OLIMEX/ESP32-P4-PC/DOCUMENTS/ESP32-P4-PC-3.jpg

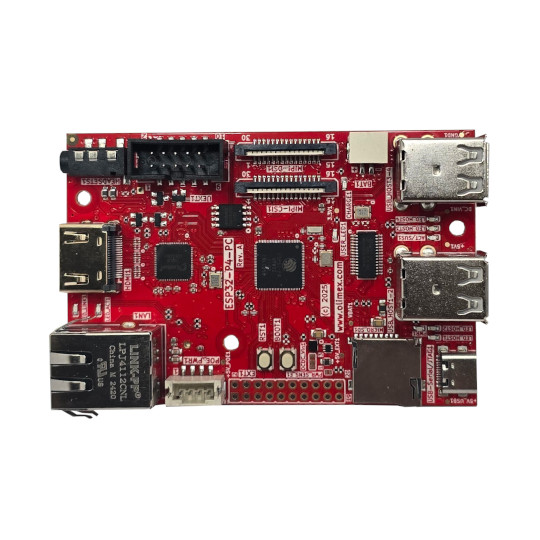
DOCUMENTS/ESP32-P4-PC-3.jpg
