OLIMEX/ESP32-P4-PC/SOFTWARE/ESP-IDF/p4_production_test/components/esp-bsp/bsp/esp32_azure_iot_kit/doc/esp32_azure_iot_kit.webp

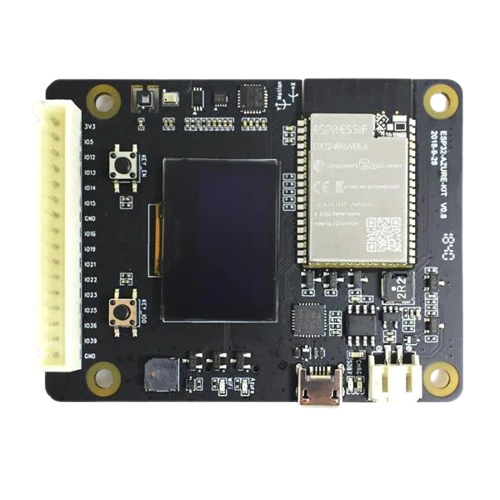
SOFTWARE/ESP-IDF/p4_production_test/components/esp-bsp/bsp/esp32_azure_iot_kit/doc/esp32_azure_iot_kit.webp
