OLIMEX/ESP32-P4-PC/SOFTWARE/ESP-IDF/p4_production_test/components/esp-bsp/bsp/esp32_azure_iot_kit/image.png

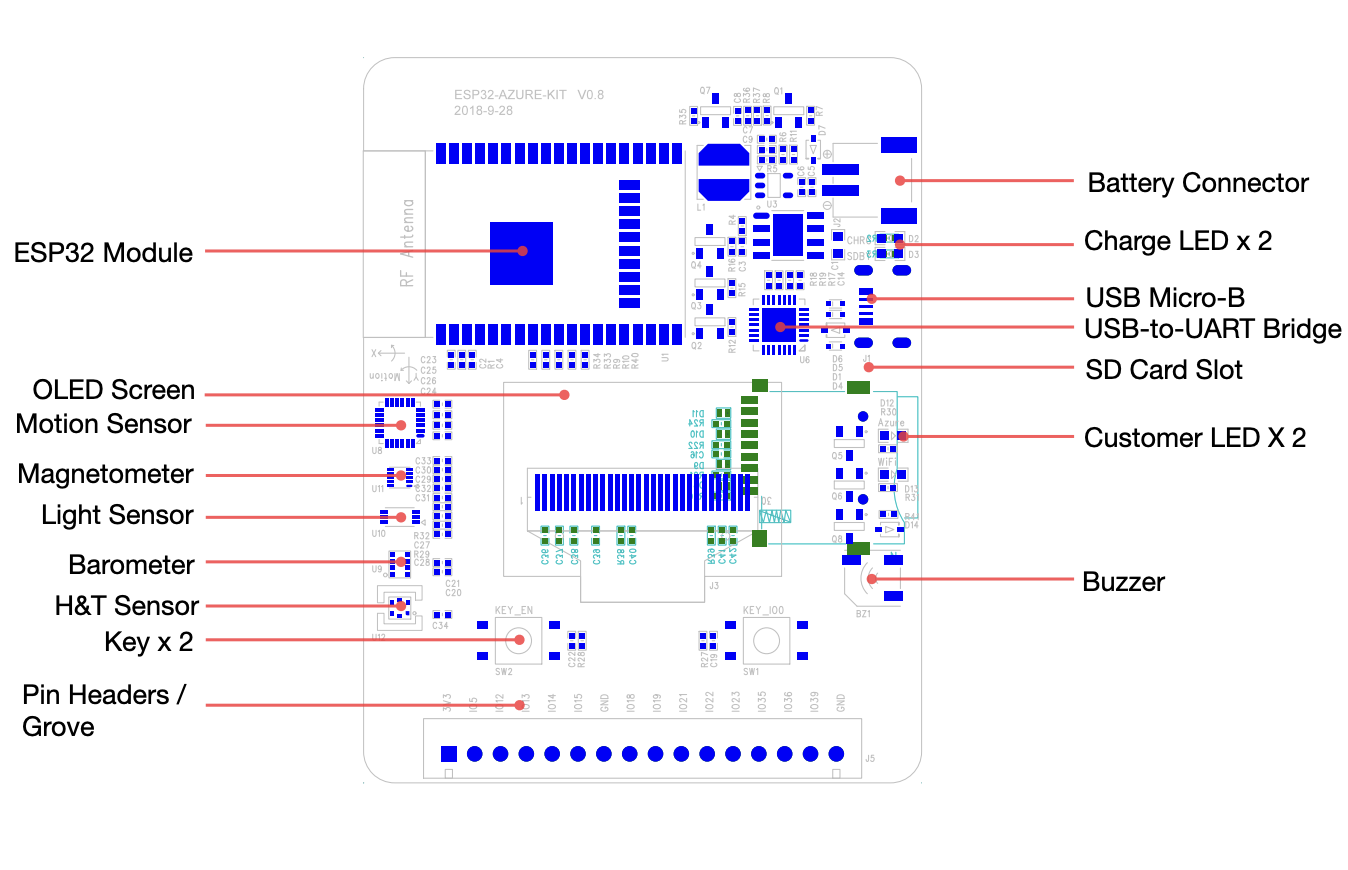
SOFTWARE/ESP-IDF/p4_production_test/components/esp-bsp/bsp/esp32_azure_iot_kit/image.png
