OLIMEX/ESP32-P4-PC/SOFTWARE/ESP-IDF/p4_production_test/components/esp-bsp/bsp/esp32_lyrat/doc/esp32_lyrat.webp

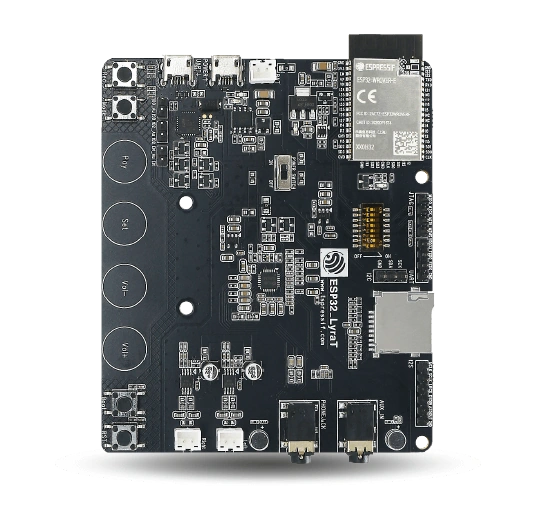
SOFTWARE/ESP-IDF/p4_production_test/components/esp-bsp/bsp/esp32_lyrat/doc/esp32_lyrat.webp
