OLIMEX/ESP32-P4-PC/SOFTWARE/ESP-IDF/p4_production_test/components/esp-bsp/bsp/esp32_lyrat/pic.jpg

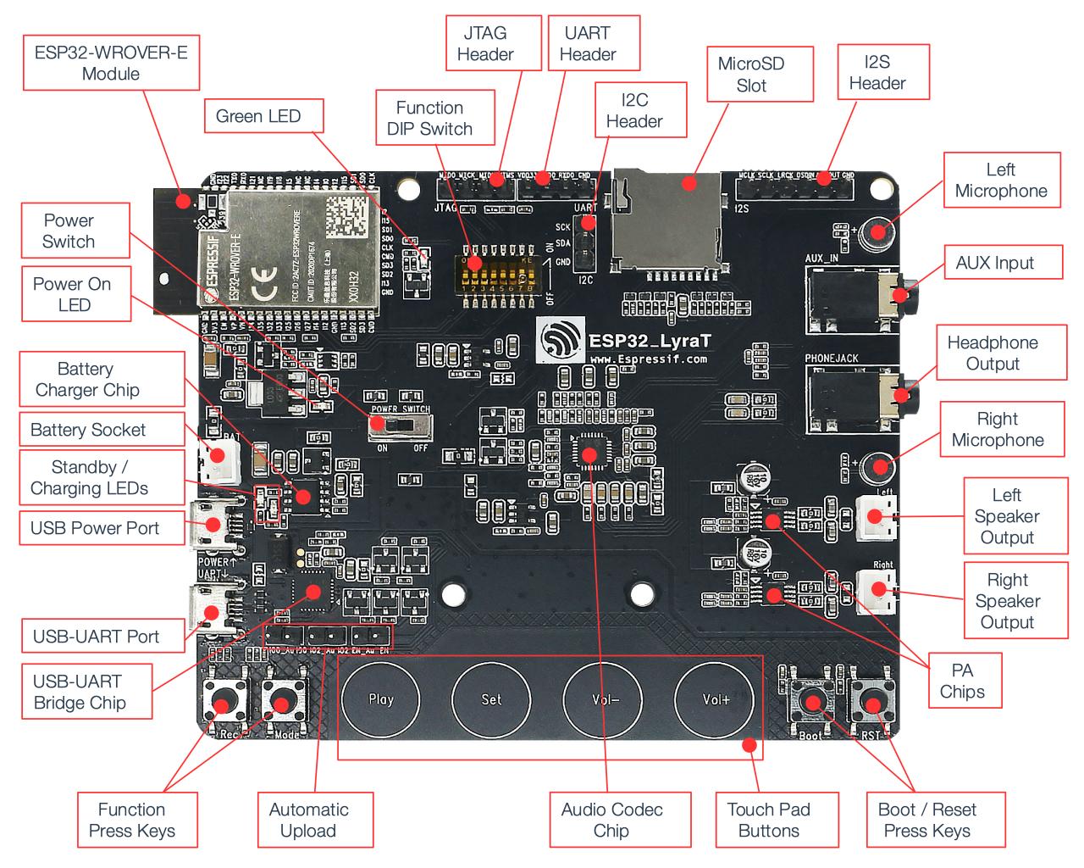
SOFTWARE/ESP-IDF/p4_production_test/components/esp-bsp/bsp/esp32_lyrat/pic.jpg
