OLIMEX/ESP32-P4-PC/SOFTWARE/ESP-IDF/p4_production_test/components/esp-bsp/bsp/esp32_p4_eye/doc/esp32_p4_eye.webp

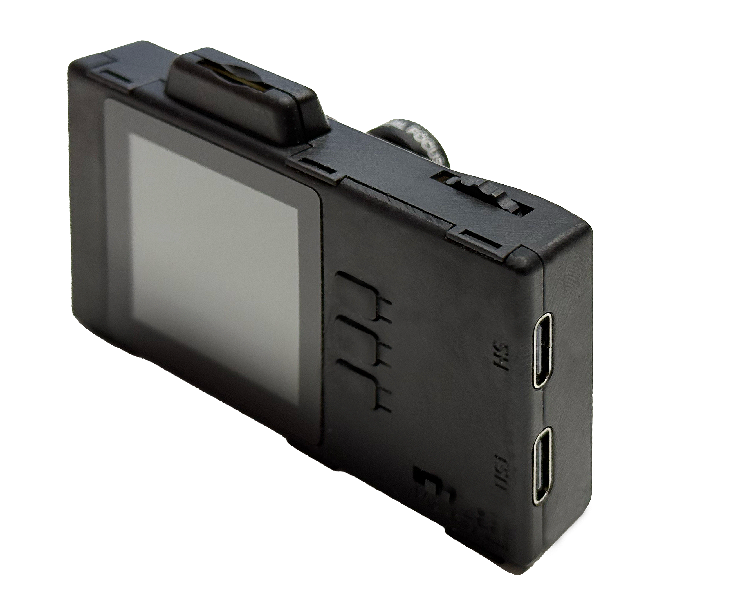
SOFTWARE/ESP-IDF/p4_production_test/components/esp-bsp/bsp/esp32_p4_eye/doc/esp32_p4_eye.webp
