OLIMEX/ESP32-P4-PC/SOFTWARE/ESP-IDF/p4_production_test/components/esp-bsp/bsp/esp32_s2_kaluga_kit/doc/esp32_s2_kaluga_kit.webp

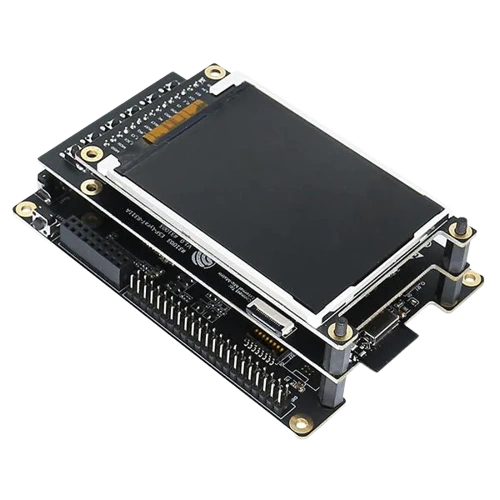
SOFTWARE/ESP-IDF/p4_production_test/components/esp-bsp/bsp/esp32_s2_kaluga_kit/doc/esp32_s2_kaluga_kit.webp
