OLIMEX/ESP32-P4-PC/SOFTWARE/ESP-IDF/p4_production_test/components/esp-bsp/bsp/esp32_s3_korvo_1/doc/esp32_s3_korvo_1.webp

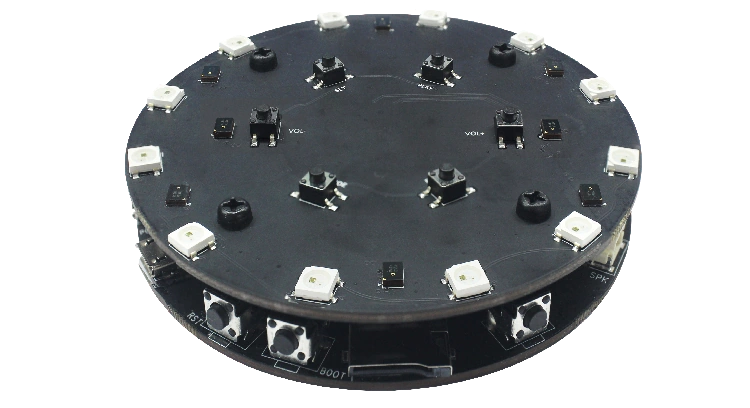
SOFTWARE/ESP-IDF/p4_production_test/components/esp-bsp/bsp/esp32_s3_korvo_1/doc/esp32_s3_korvo_1.webp
