OLIMEX/ESP32-P4-PC/SOFTWARE/ESP-IDF/p4_production_test/components/esp-bsp/bsp/esp32_s3_lcd_ev_board/doc/esp32_s3_lcd_ev_board.webp

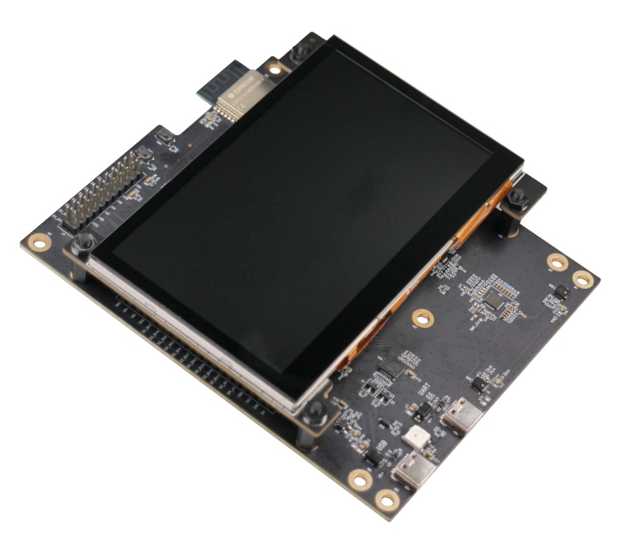
SOFTWARE/ESP-IDF/p4_production_test/components/esp-bsp/bsp/esp32_s3_lcd_ev_board/doc/esp32_s3_lcd_ev_board.webp
