OLIMEX/ESP32-P4-PC/SOFTWARE/ESP-IDF/p4_production_test/components/esp-bsp/bsp/esp_wrover_kit/doc/esp-wrover-kit-v4.1-layout-front.png

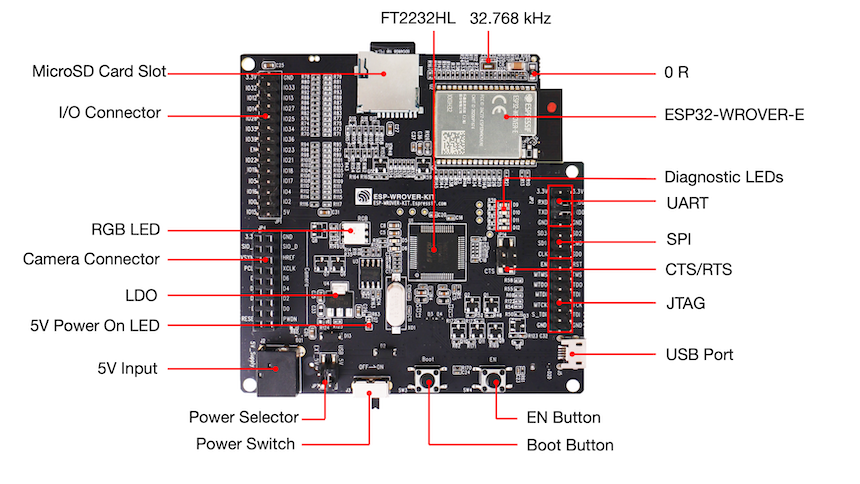
SOFTWARE/ESP-IDF/p4_production_test/components/esp-bsp/bsp/esp_wrover_kit/doc/esp-wrover-kit-v4.1-layout-front.png
