OLIMEX/ESP32-P4-PC/SOFTWARE/ESP-IDF/p4_production_test/components/esp-bsp/bsp/esp_wrover_kit/doc/esp_wrover_kit.webp

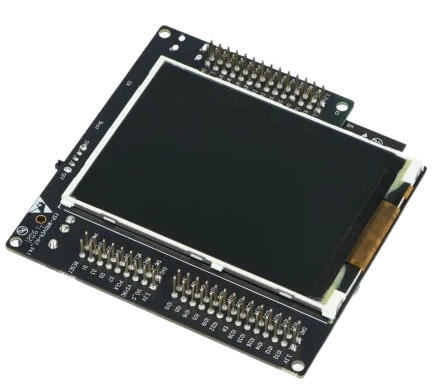
SOFTWARE/ESP-IDF/p4_production_test/components/esp-bsp/bsp/esp_wrover_kit/doc/esp_wrover_kit.webp
