OLIMEX/ESP32-P4-PC/SOFTWARE/ESP-IDF/p4_production_test/components/esp-bsp/bsp/m5_atom_s3/doc/m5_atom_s3.webp

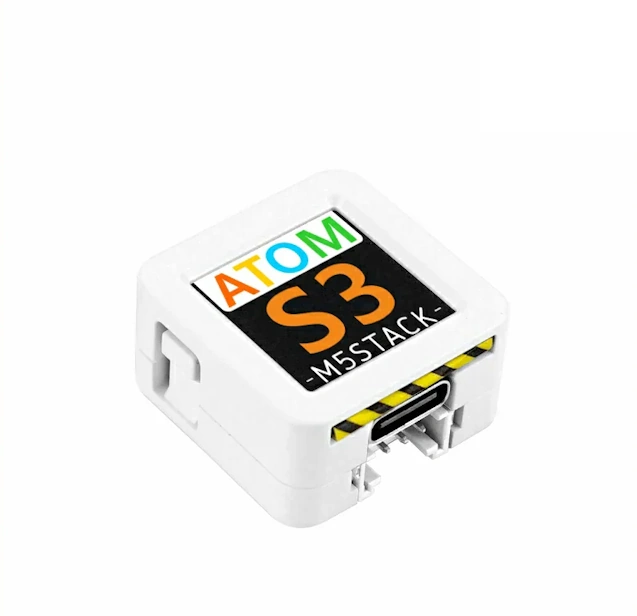
SOFTWARE/ESP-IDF/p4_production_test/components/esp-bsp/bsp/m5_atom_s3/doc/m5_atom_s3.webp
