OLIMEX/ESP32-P4-PC/SOFTWARE/ESP-IDF/p4_production_test/components/esp-bsp/bsp/m5dial/doc/m5dial.webp

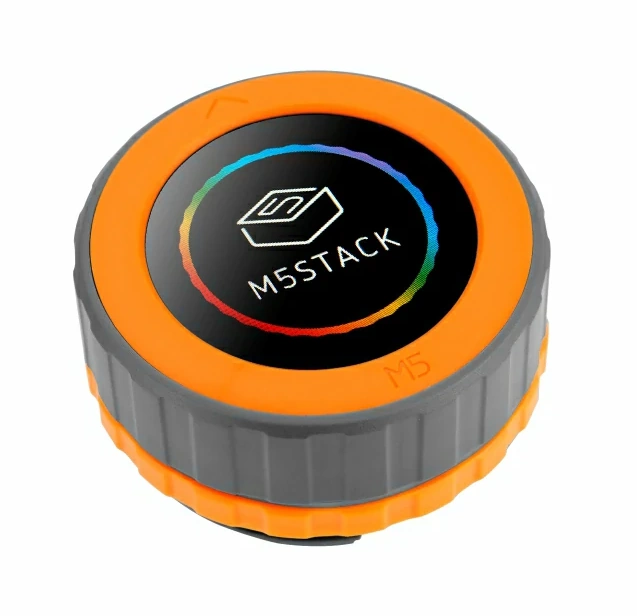
SOFTWARE/ESP-IDF/p4_production_test/components/esp-bsp/bsp/m5dial/doc/m5dial.webp
