OLIMEX/ESP32-P4-PC/SOFTWARE/ESP-IDF/p4_production_test/components/esp-bsp/bsp/m5dial/doc/pic.webp

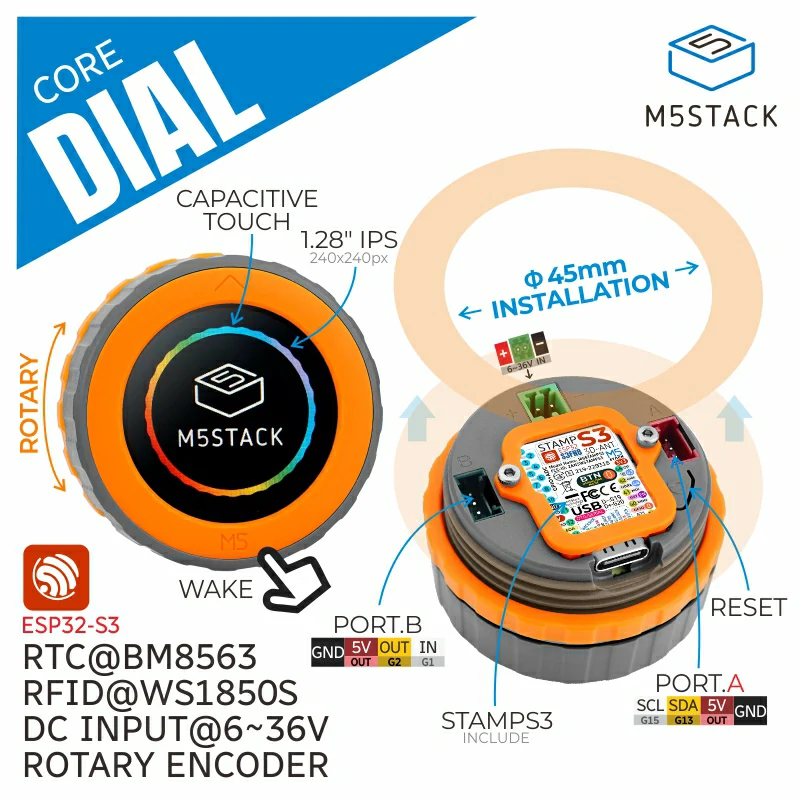
SOFTWARE/ESP-IDF/p4_production_test/components/esp-bsp/bsp/m5dial/doc/pic.webp
