OLIMEX/ESP32-P4-PC/SOFTWARE/ESP-IDF/p4_production_test/components/esp-bsp/bsp/m5stack_core_s3/doc/pic.webp

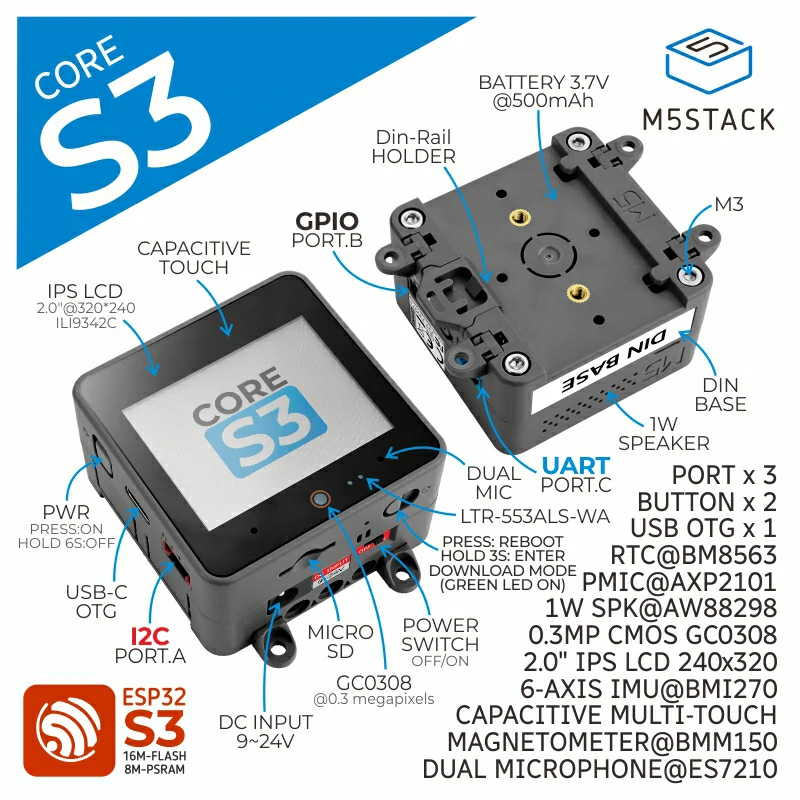
SOFTWARE/ESP-IDF/p4_production_test/components/esp-bsp/bsp/m5stack_core_s3/doc/pic.webp
