OLIMEX/ESP32-P4-PC/SOFTWARE/ESP-IDF/p4_production_test/components/esp-bsp/components/esp_lvgl_port/docs/frame_buffer_settings.png

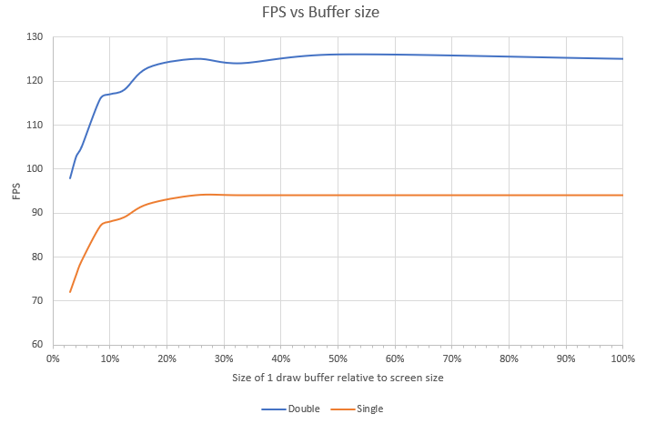
SOFTWARE/ESP-IDF/p4_production_test/components/esp-bsp/components/esp_lvgl_port/docs/frame_buffer_settings.png
