OLIMEX/ESP32-P4-PC/SOFTWARE/ESP-IDF/p4_production_test/components/esp-bsp/docu/pics/1.3inch-oled-module-c-1.jpg

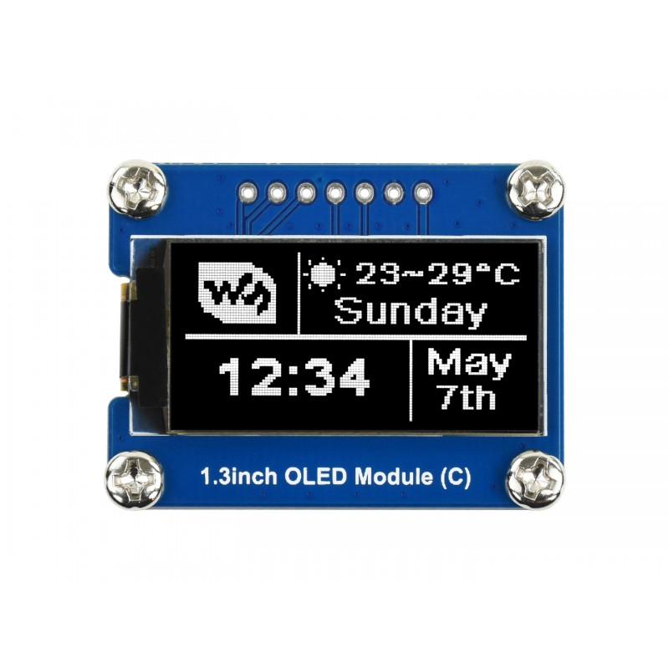
SOFTWARE/ESP-IDF/p4_production_test/components/esp-bsp/docu/pics/1.3inch-oled-module-c-1.jpg
