OLIMEX/ESP32-P4-PC/SOFTWARE/ESP-IDF/p4_production_test/components/esp-bsp/docu/pics/1.28inch-LCD-Module-1.jpg

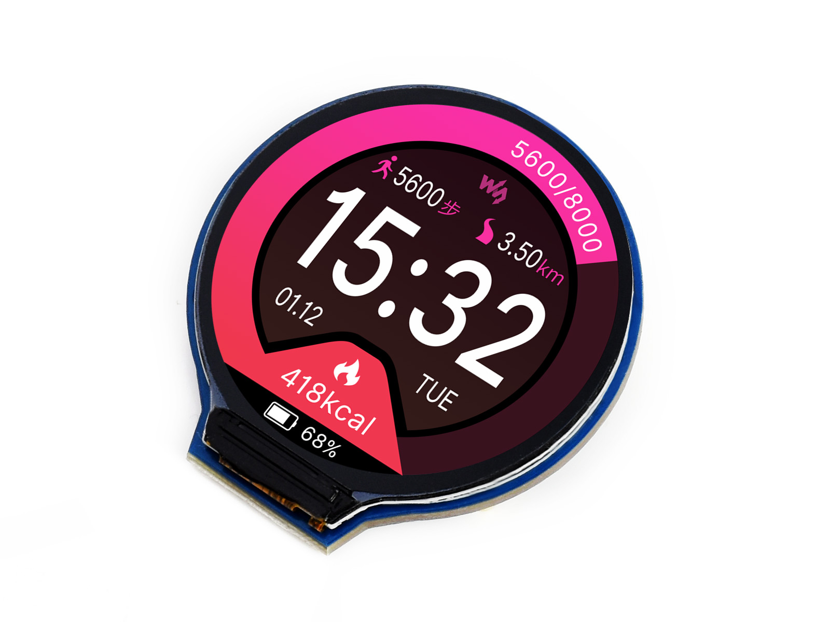
SOFTWARE/ESP-IDF/p4_production_test/components/esp-bsp/docu/pics/1.28inch-LCD-Module-1.jpg
