OLIMEX/ESP32-P4-PC/SOFTWARE/ESP-IDF/p4_production_test/components/esp-bsp/docu/pics/7inch-Capacitive-Touch-LCD-C_l.jpg

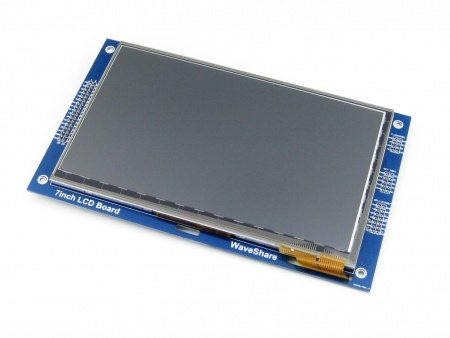
SOFTWARE/ESP-IDF/p4_production_test/components/esp-bsp/docu/pics/7inch-Capacitive-Touch-LCD-C_l.jpg
