OLIMEX/ESP32-P4-PC/SOFTWARE/ESP-IDF/p4_production_test/components/esp-bsp/docu/pics/Adafruit-PiTFT.jpg

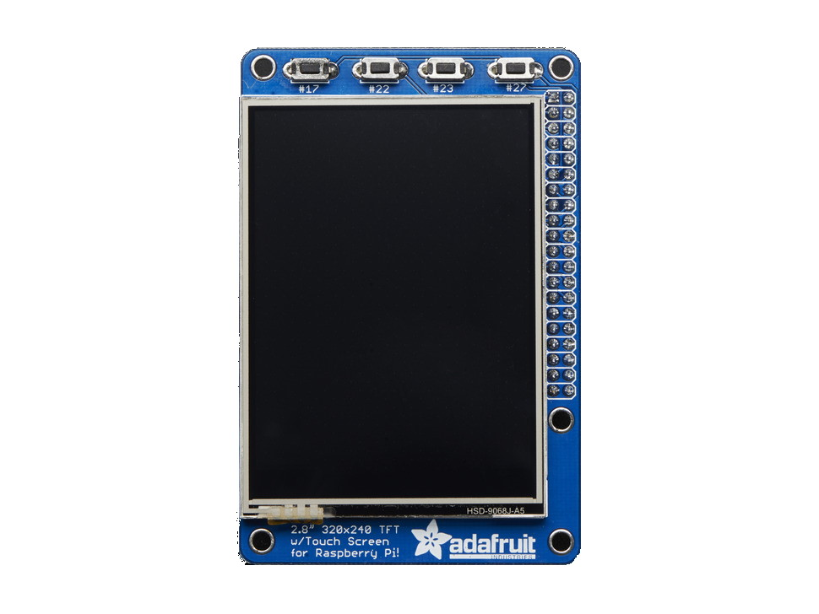
SOFTWARE/ESP-IDF/p4_production_test/components/esp-bsp/docu/pics/Adafruit-PiTFT.jpg
