OLIMEX/ESP32-P4-PC/SOFTWARE/ESP-IDF/p4_production_test/components/esp-bsp/docu/pics/esp32-s2-hmi-devkit-1-3d-v1.0.png

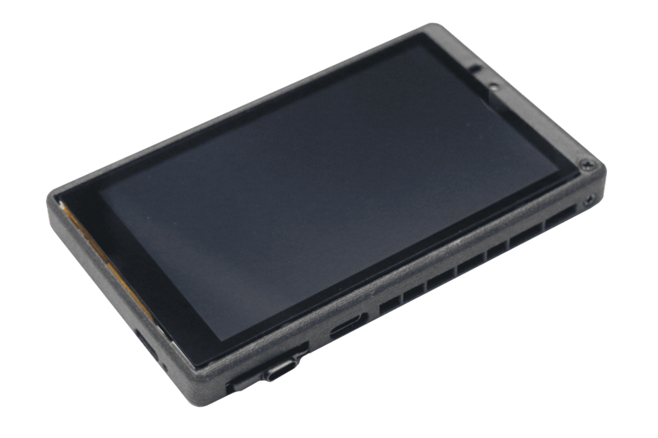
SOFTWARE/ESP-IDF/p4_production_test/components/esp-bsp/docu/pics/esp32-s2-hmi-devkit-1-3d-v1.0.png
