OLIMEX/ESP32-P4-PC/SOFTWARE/ESP-IDF/p4_production_test/components/esp-bsp/docu/pics/ili9488-parallel.webp

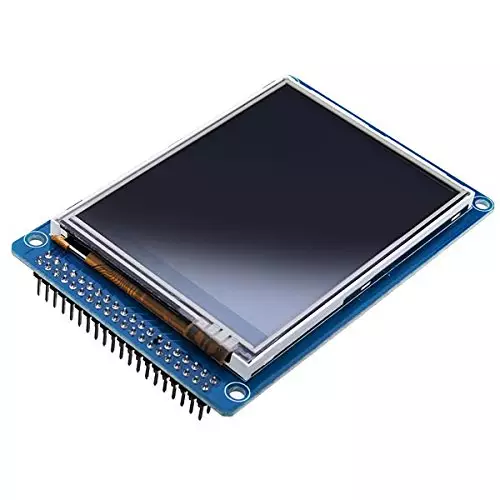
SOFTWARE/ESP-IDF/p4_production_test/components/esp-bsp/docu/pics/ili9488-parallel.webp
