OLIMEX/ESP32-P4-PC/SOFTWARE/ESP-IDF/p4_production_test/components/esp-bsp/docu/pics/Lontium.webp

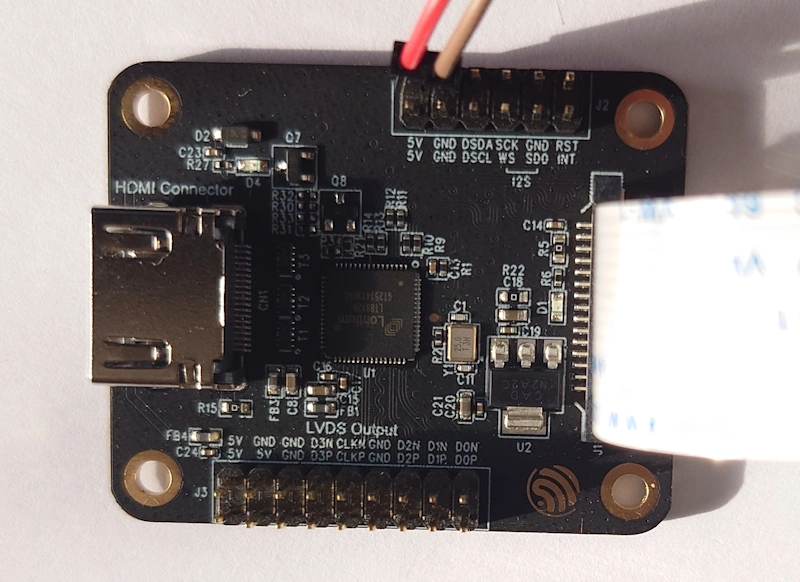
SOFTWARE/ESP-IDF/p4_production_test/components/esp-bsp/docu/pics/Lontium.webp
