OLIMEX/ESP32-P4-PC/SOFTWARE/ESP-IDF/p4_production_test/components/esp-bsp/docu/pics/ssd1306.jpg

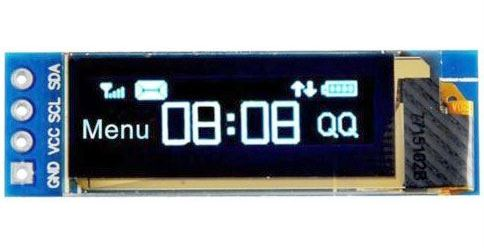
SOFTWARE/ESP-IDF/p4_production_test/components/esp-bsp/docu/pics/ssd1306.jpg
