OLIMEX/ESP32-P4-PC/SOFTWARE/ESP-IDF/p4_production_test/components/esp-bsp/docu/pics/st7796.jpg

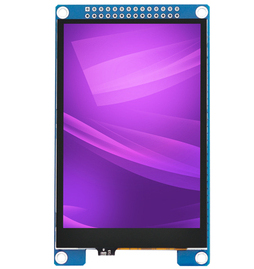
SOFTWARE/ESP-IDF/p4_production_test/components/esp-bsp/docu/pics/st7796.jpg
