OLIMEX/ESP32-P4-PC/SOFTWARE/ESP-IDF/p4_production_test/components/esp-bsp/examples/display_audio_photo/doc/pic.webp

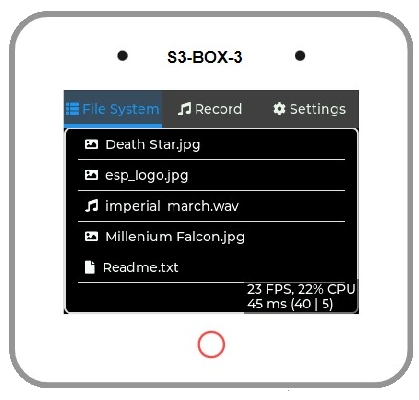
SOFTWARE/ESP-IDF/p4_production_test/components/esp-bsp/examples/display_audio_photo/doc/pic.webp
