OLIMEX/ESP32-P4-PC/SOFTWARE/ESP-IDF/p4_production_test/components/esp-bsp/examples/display_audio_photo/spiffs_content/Millenium Falcon.jpg

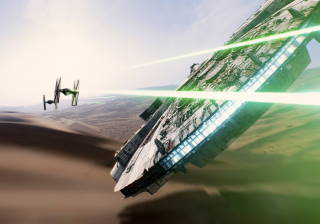
SOFTWARE/ESP-IDF/p4_production_test/components/esp-bsp/examples/display_audio_photo/spiffs_content/Millenium Falcon.jpg
