OLIMEX/ESP32-P4-PC/SOFTWARE/ESP-IDF/p4_production_test/components/esp-bsp/SquareLine/boards/v9/esp32_c3_lcdkit/image.png

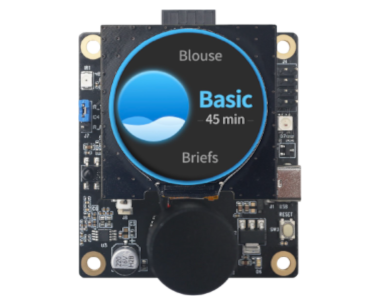
SOFTWARE/ESP-IDF/p4_production_test/components/esp-bsp/SquareLine/boards/v9/esp32_c3_lcdkit/image.png
