OLIMEX/ESP32-P4-PC/SOFTWARE/ESP-IDF/p4_production_test/components/esp-bsp/SquareLine/boards/v9/esp32_s3_eye/image.png

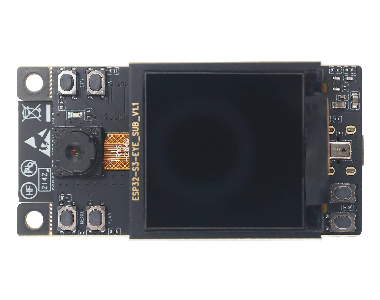
SOFTWARE/ESP-IDF/p4_production_test/components/esp-bsp/SquareLine/boards/v9/esp32_s3_eye/image.png
