OLIMEX/ESP32-P4-PC/SOFTWARE/Ardunio/ESP32-P4-PC-and-USB-LTE4G-EU/Hardware-setup-2.jpg

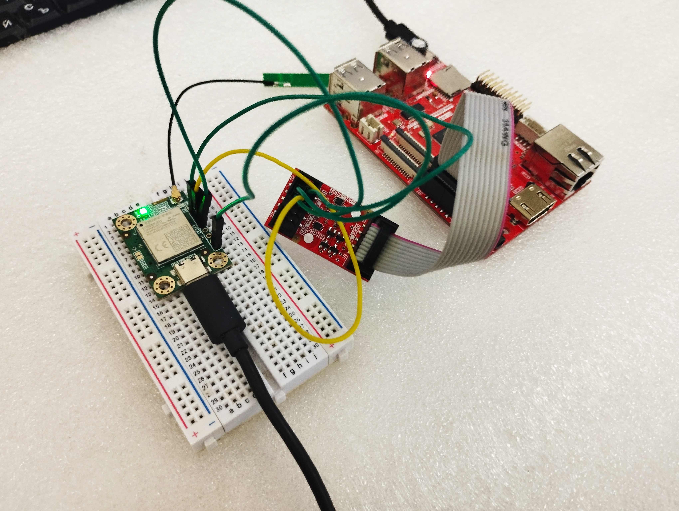
SOFTWARE/Ardunio/ESP32-P4-PC-and-USB-LTE4G-EU/Hardware-setup-2.jpg
