OLIMEX/ESP32-P4-PC/SOFTWARE/ESP-IDF/p4_production_test/components/esp-bsp/test_apps/noglib/image.jpg

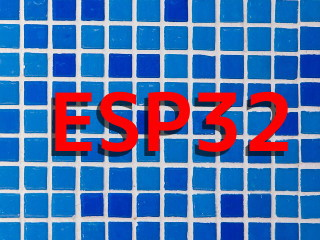
SOFTWARE/ESP-IDF/p4_production_test/components/esp-bsp/test_apps/noglib/image.jpg
