OLIMEX/ESP32-P4-PC/HARDWARE/ESP32-P4-PC-Rev.B/ESP32-P4-PC_Rev_B.kicad_sch

## KiCad design HARDWARE/ESP32-P4-PC-Rev.B/ESP32-P4-PC_Rev_B.kicad_sch (2026-02-17)

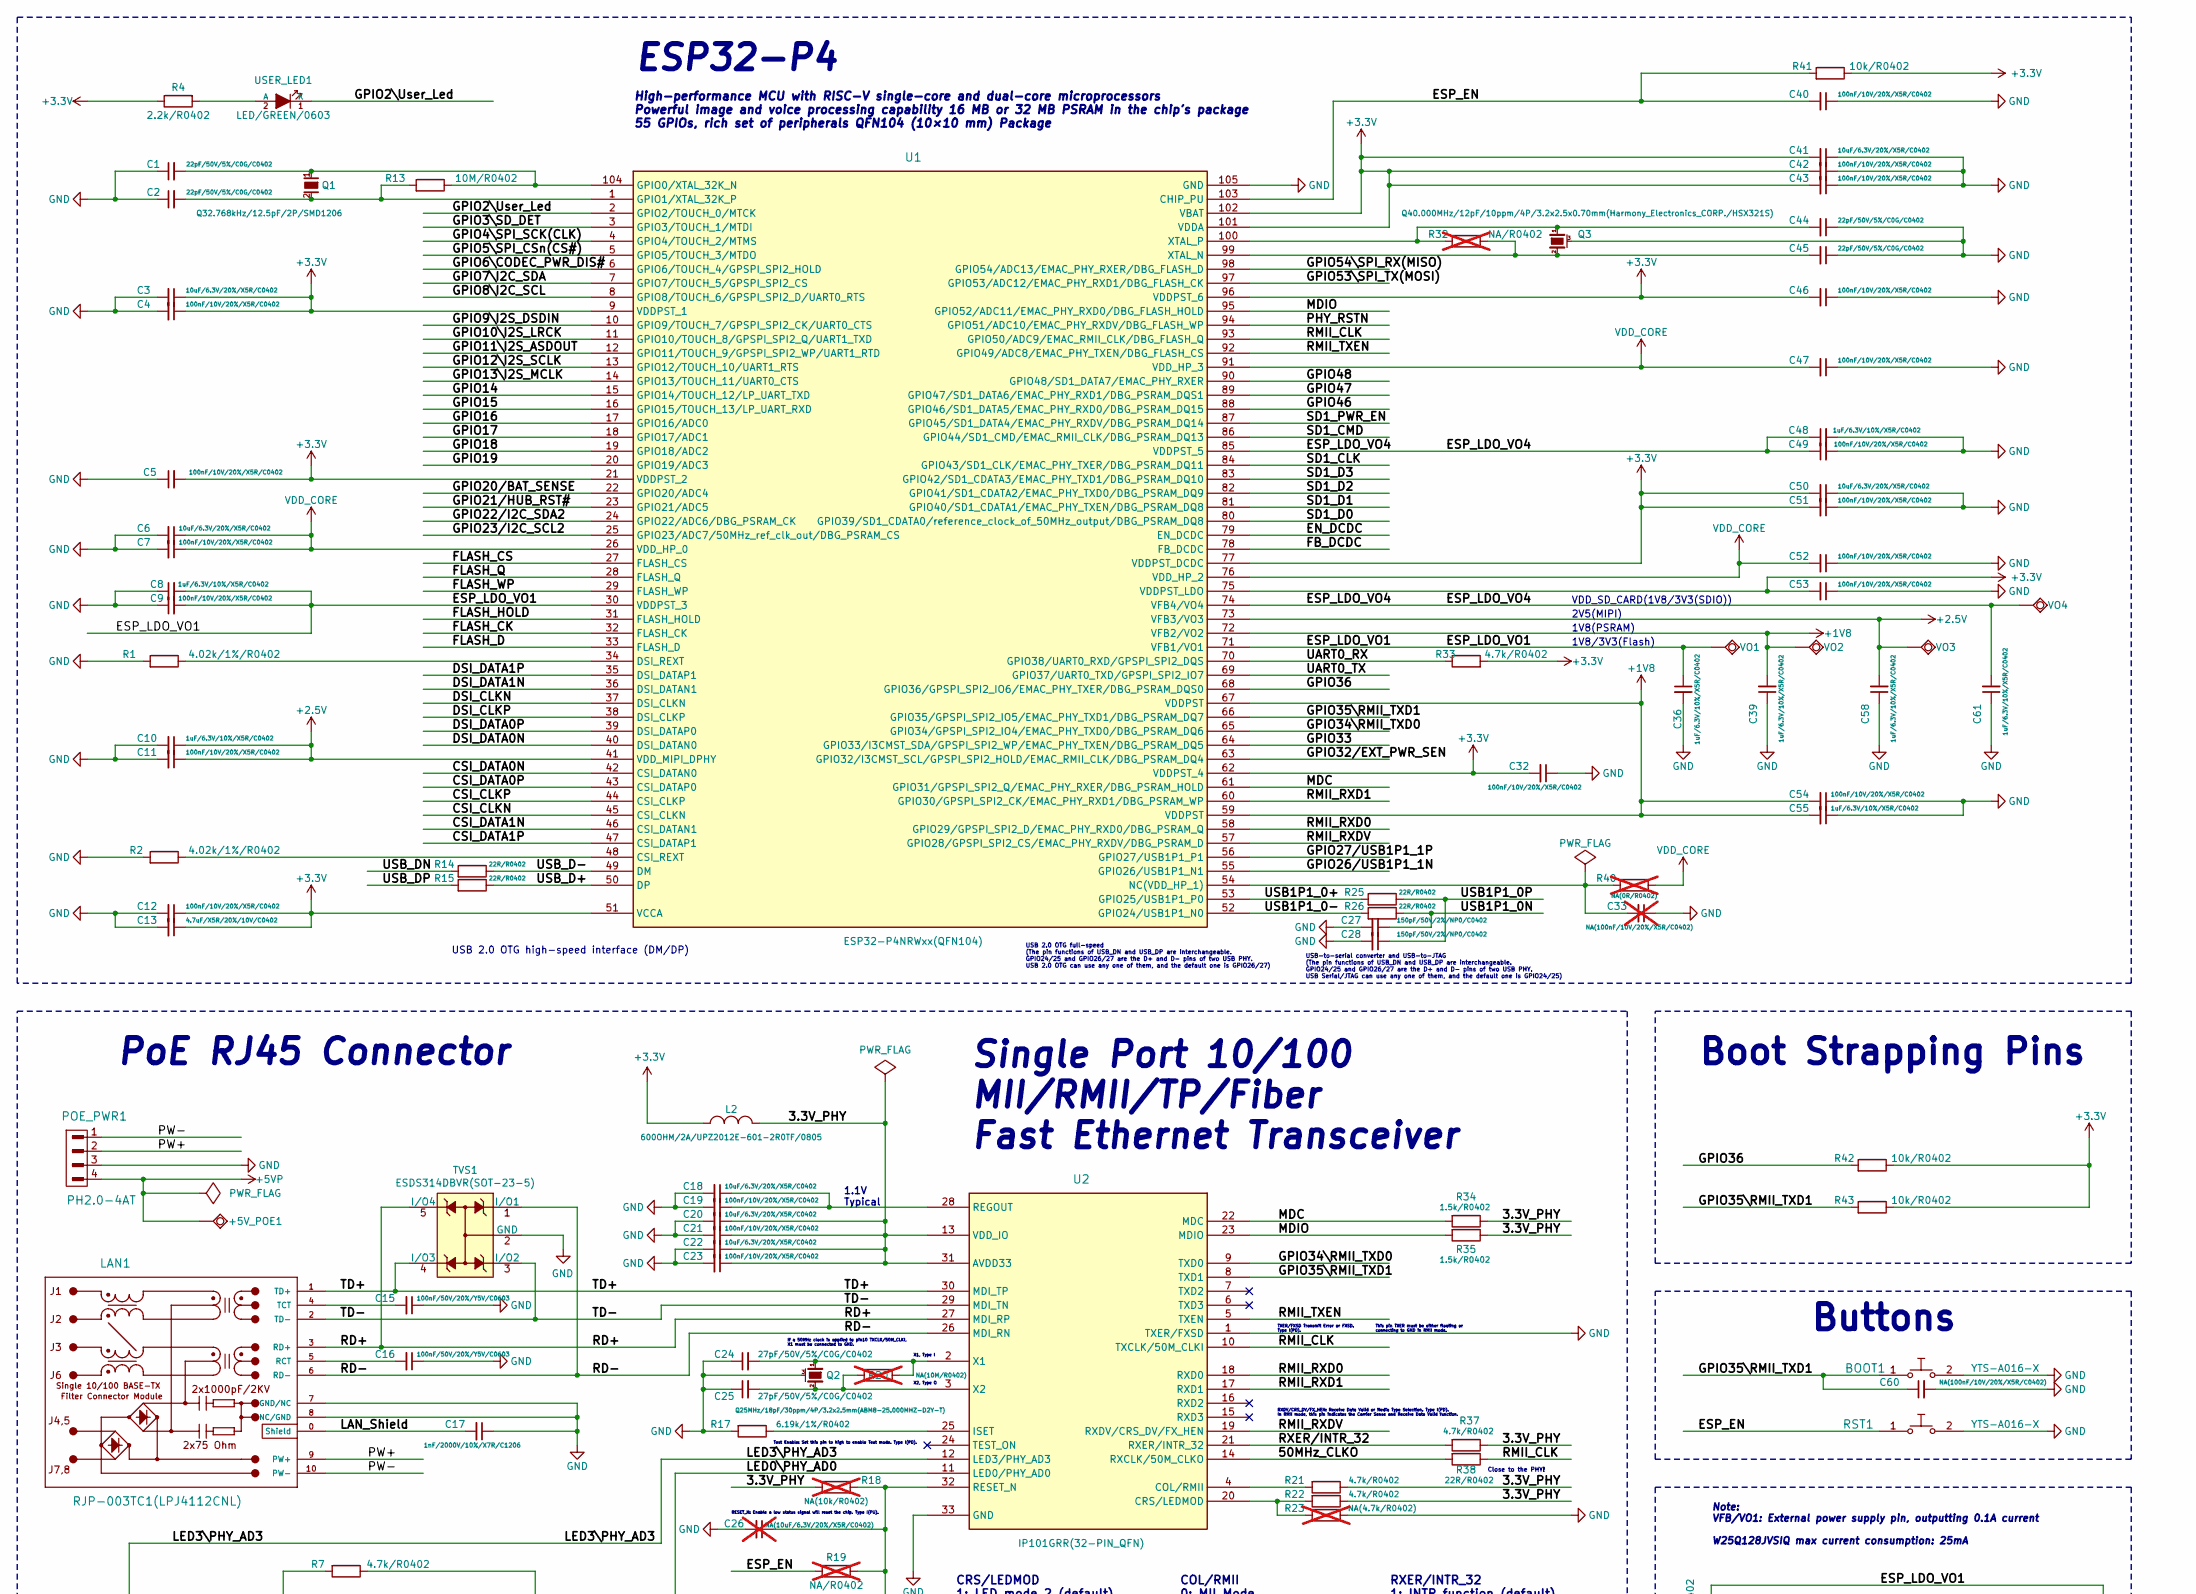
[picture p87: schematic ESP32-P4-PC_Rev_B.kicad_sch, part in row 1, column 1]

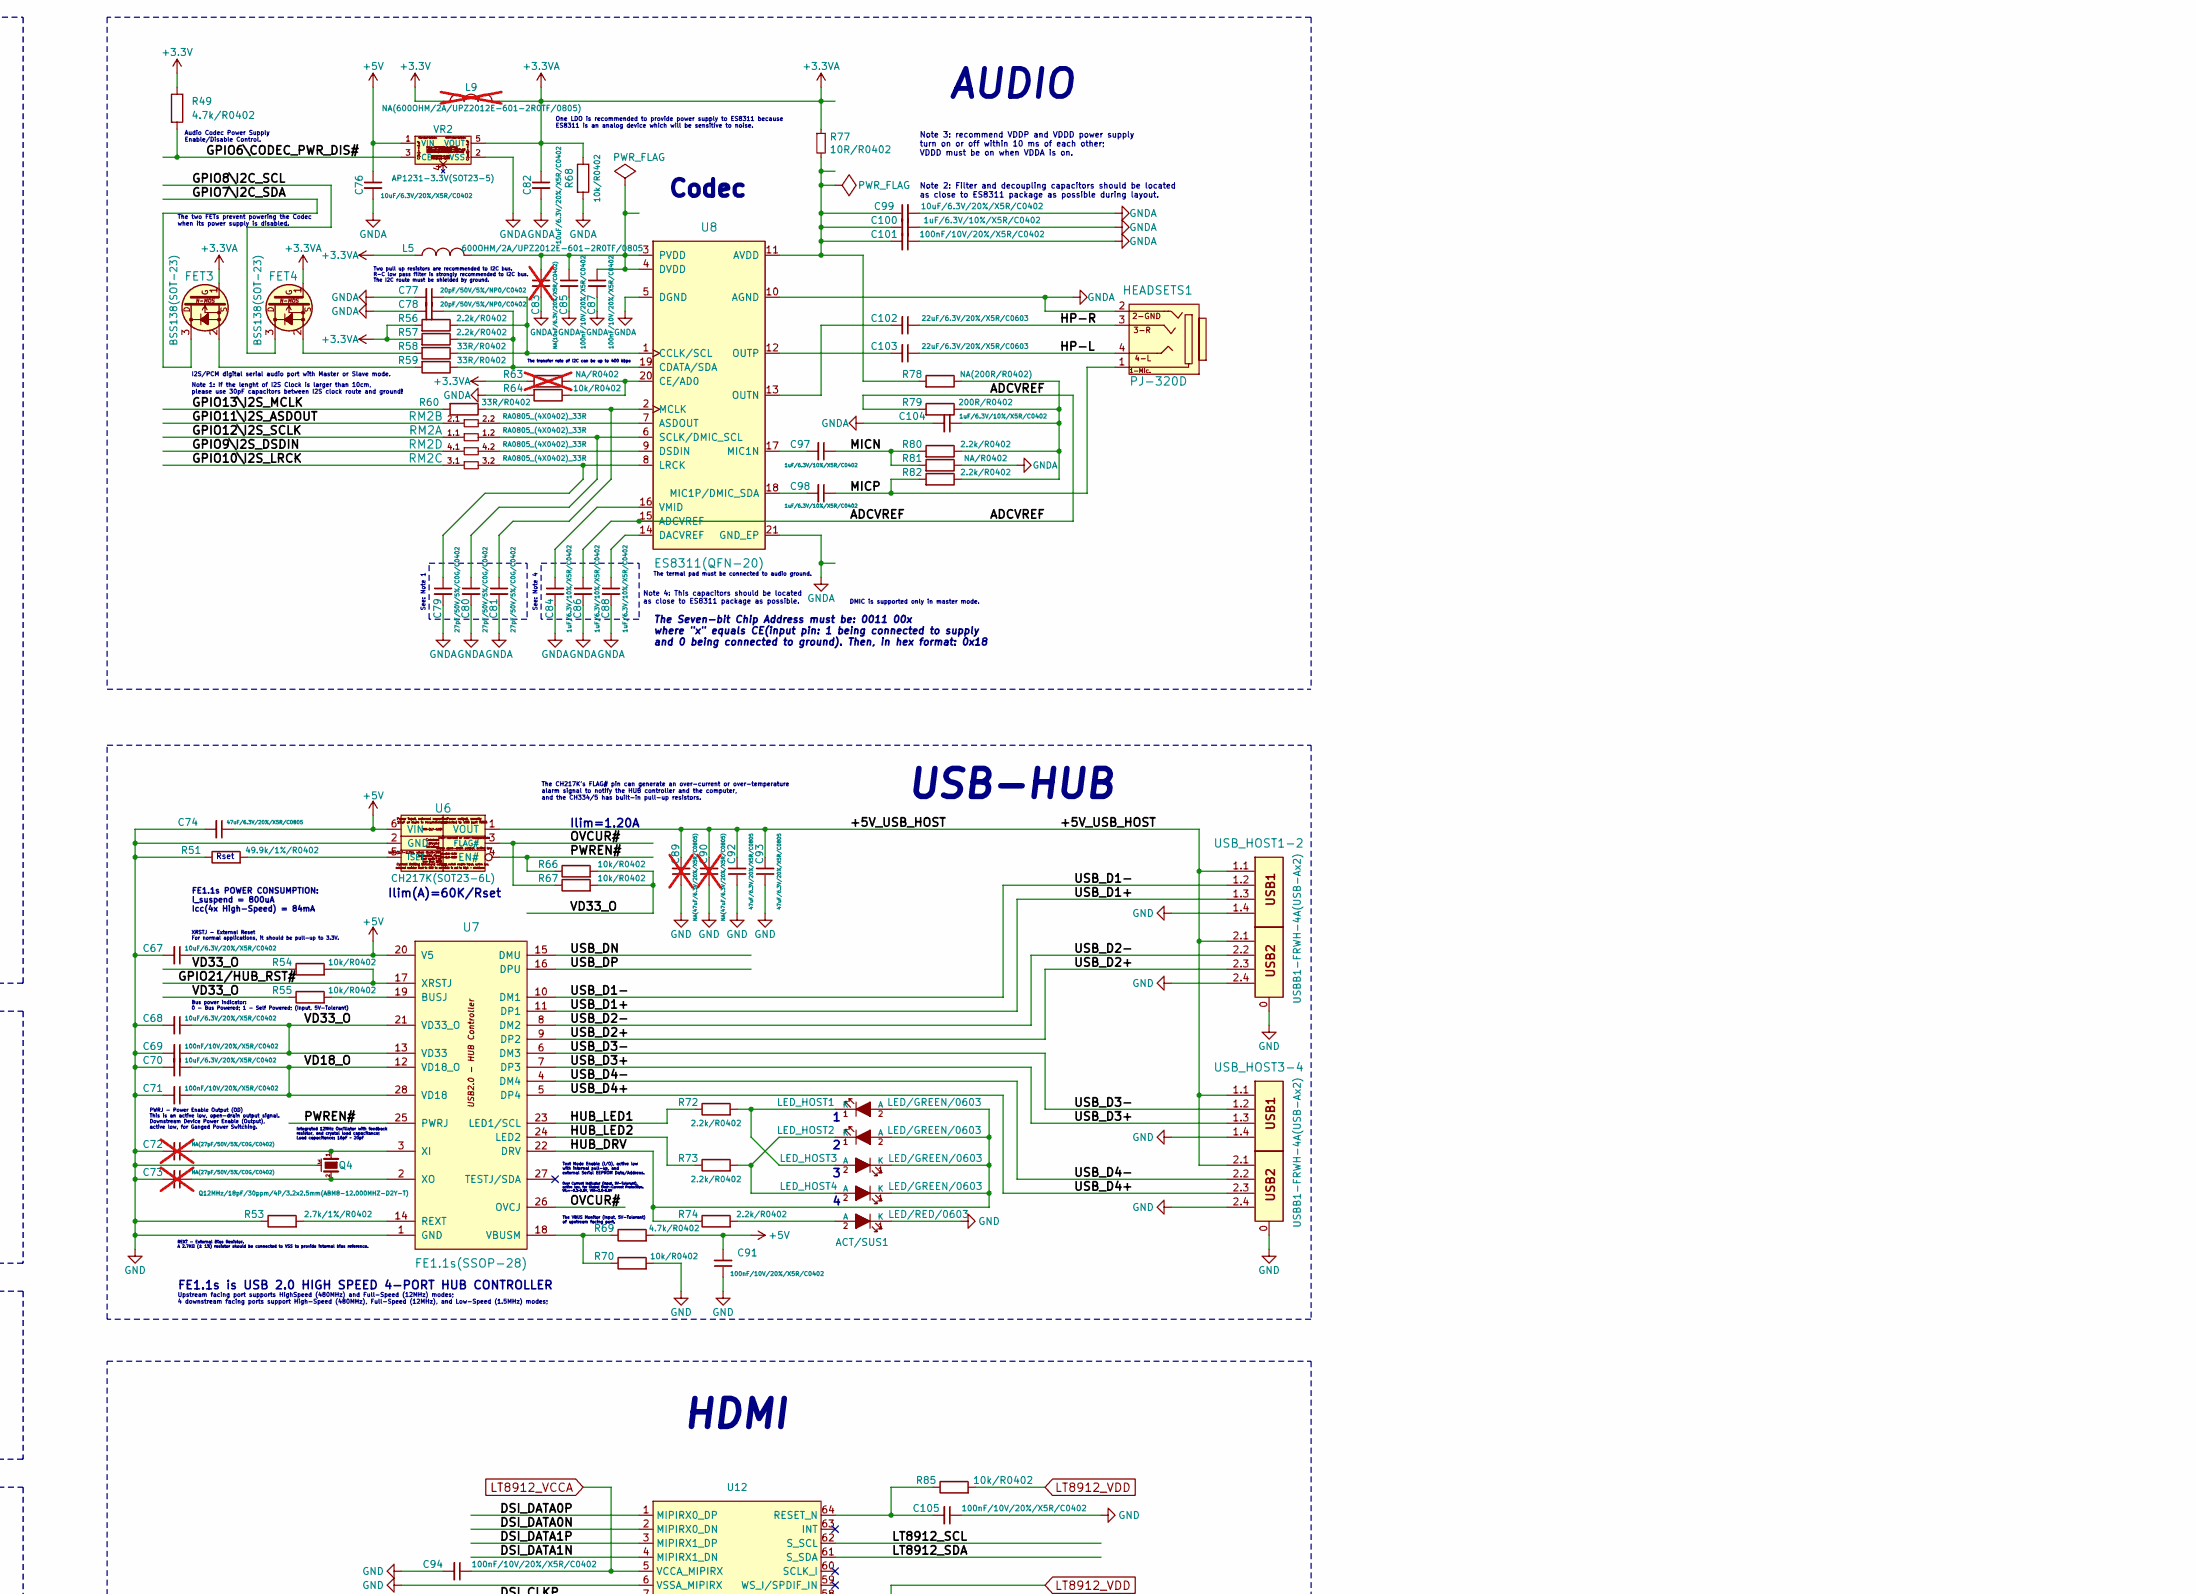
[picture p88: schematic ESP32-P4-PC_Rev_B.kicad_sch, part in row 1, column 2]

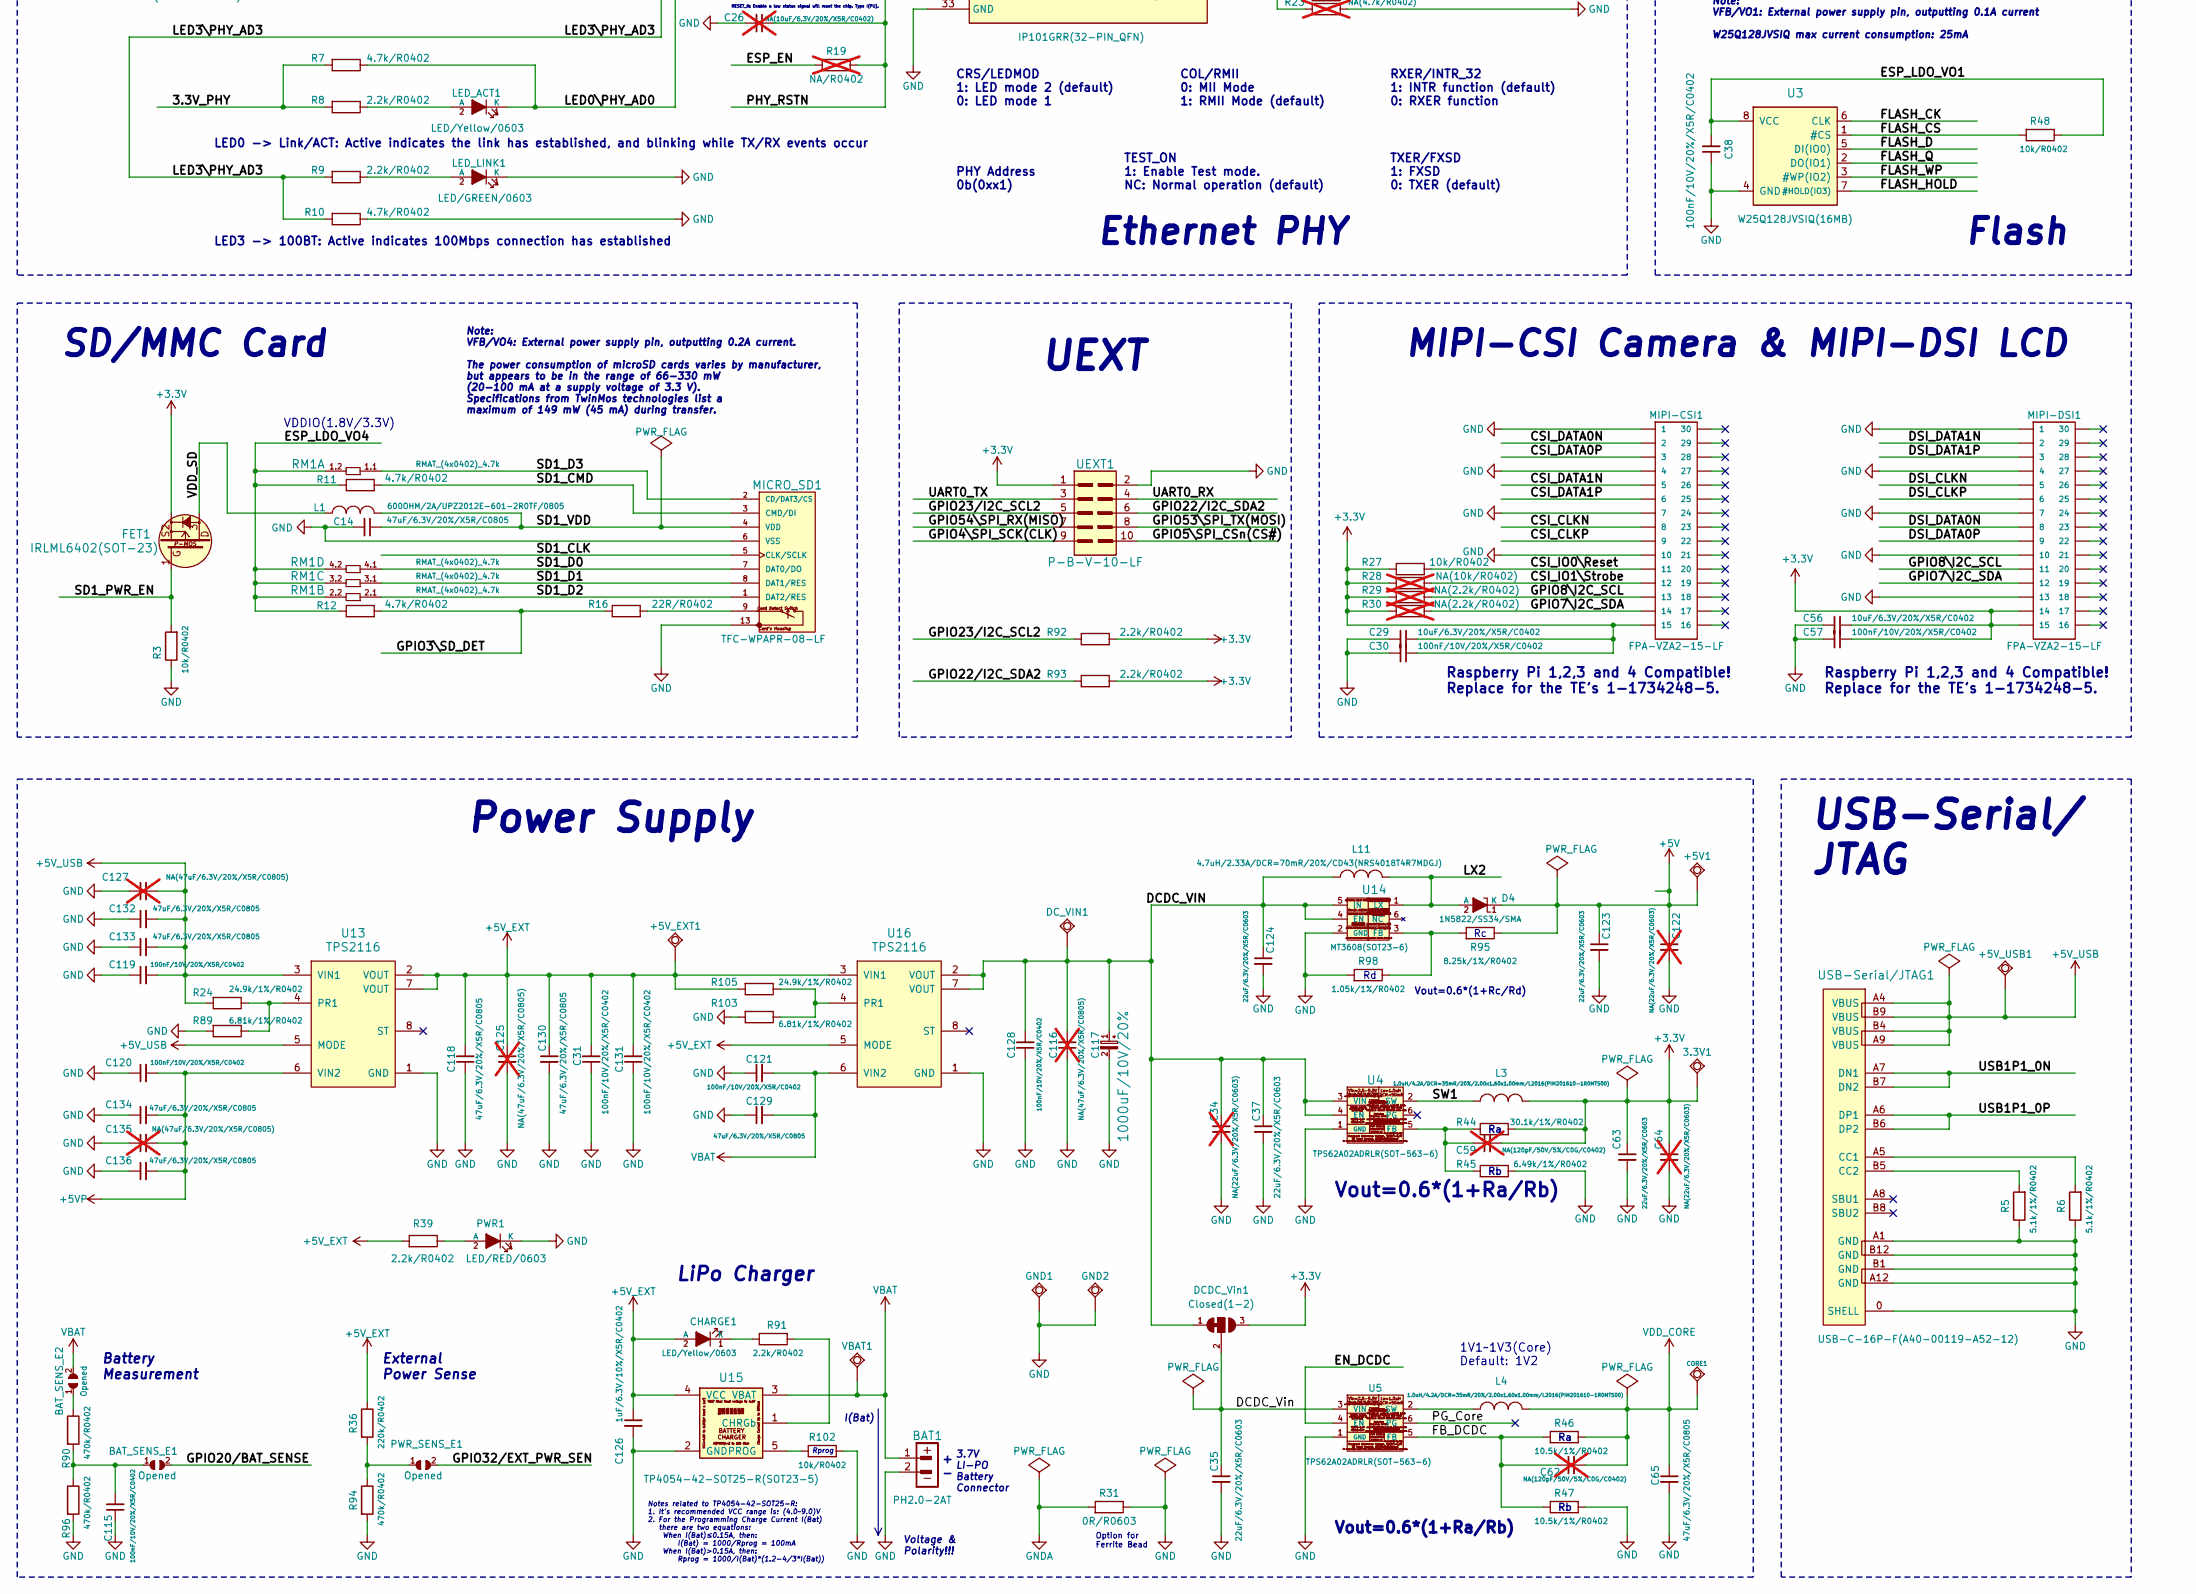
[picture p89: schematic ESP32-P4-PC_Rev_B.kicad_sch, part in row 2, column 1]

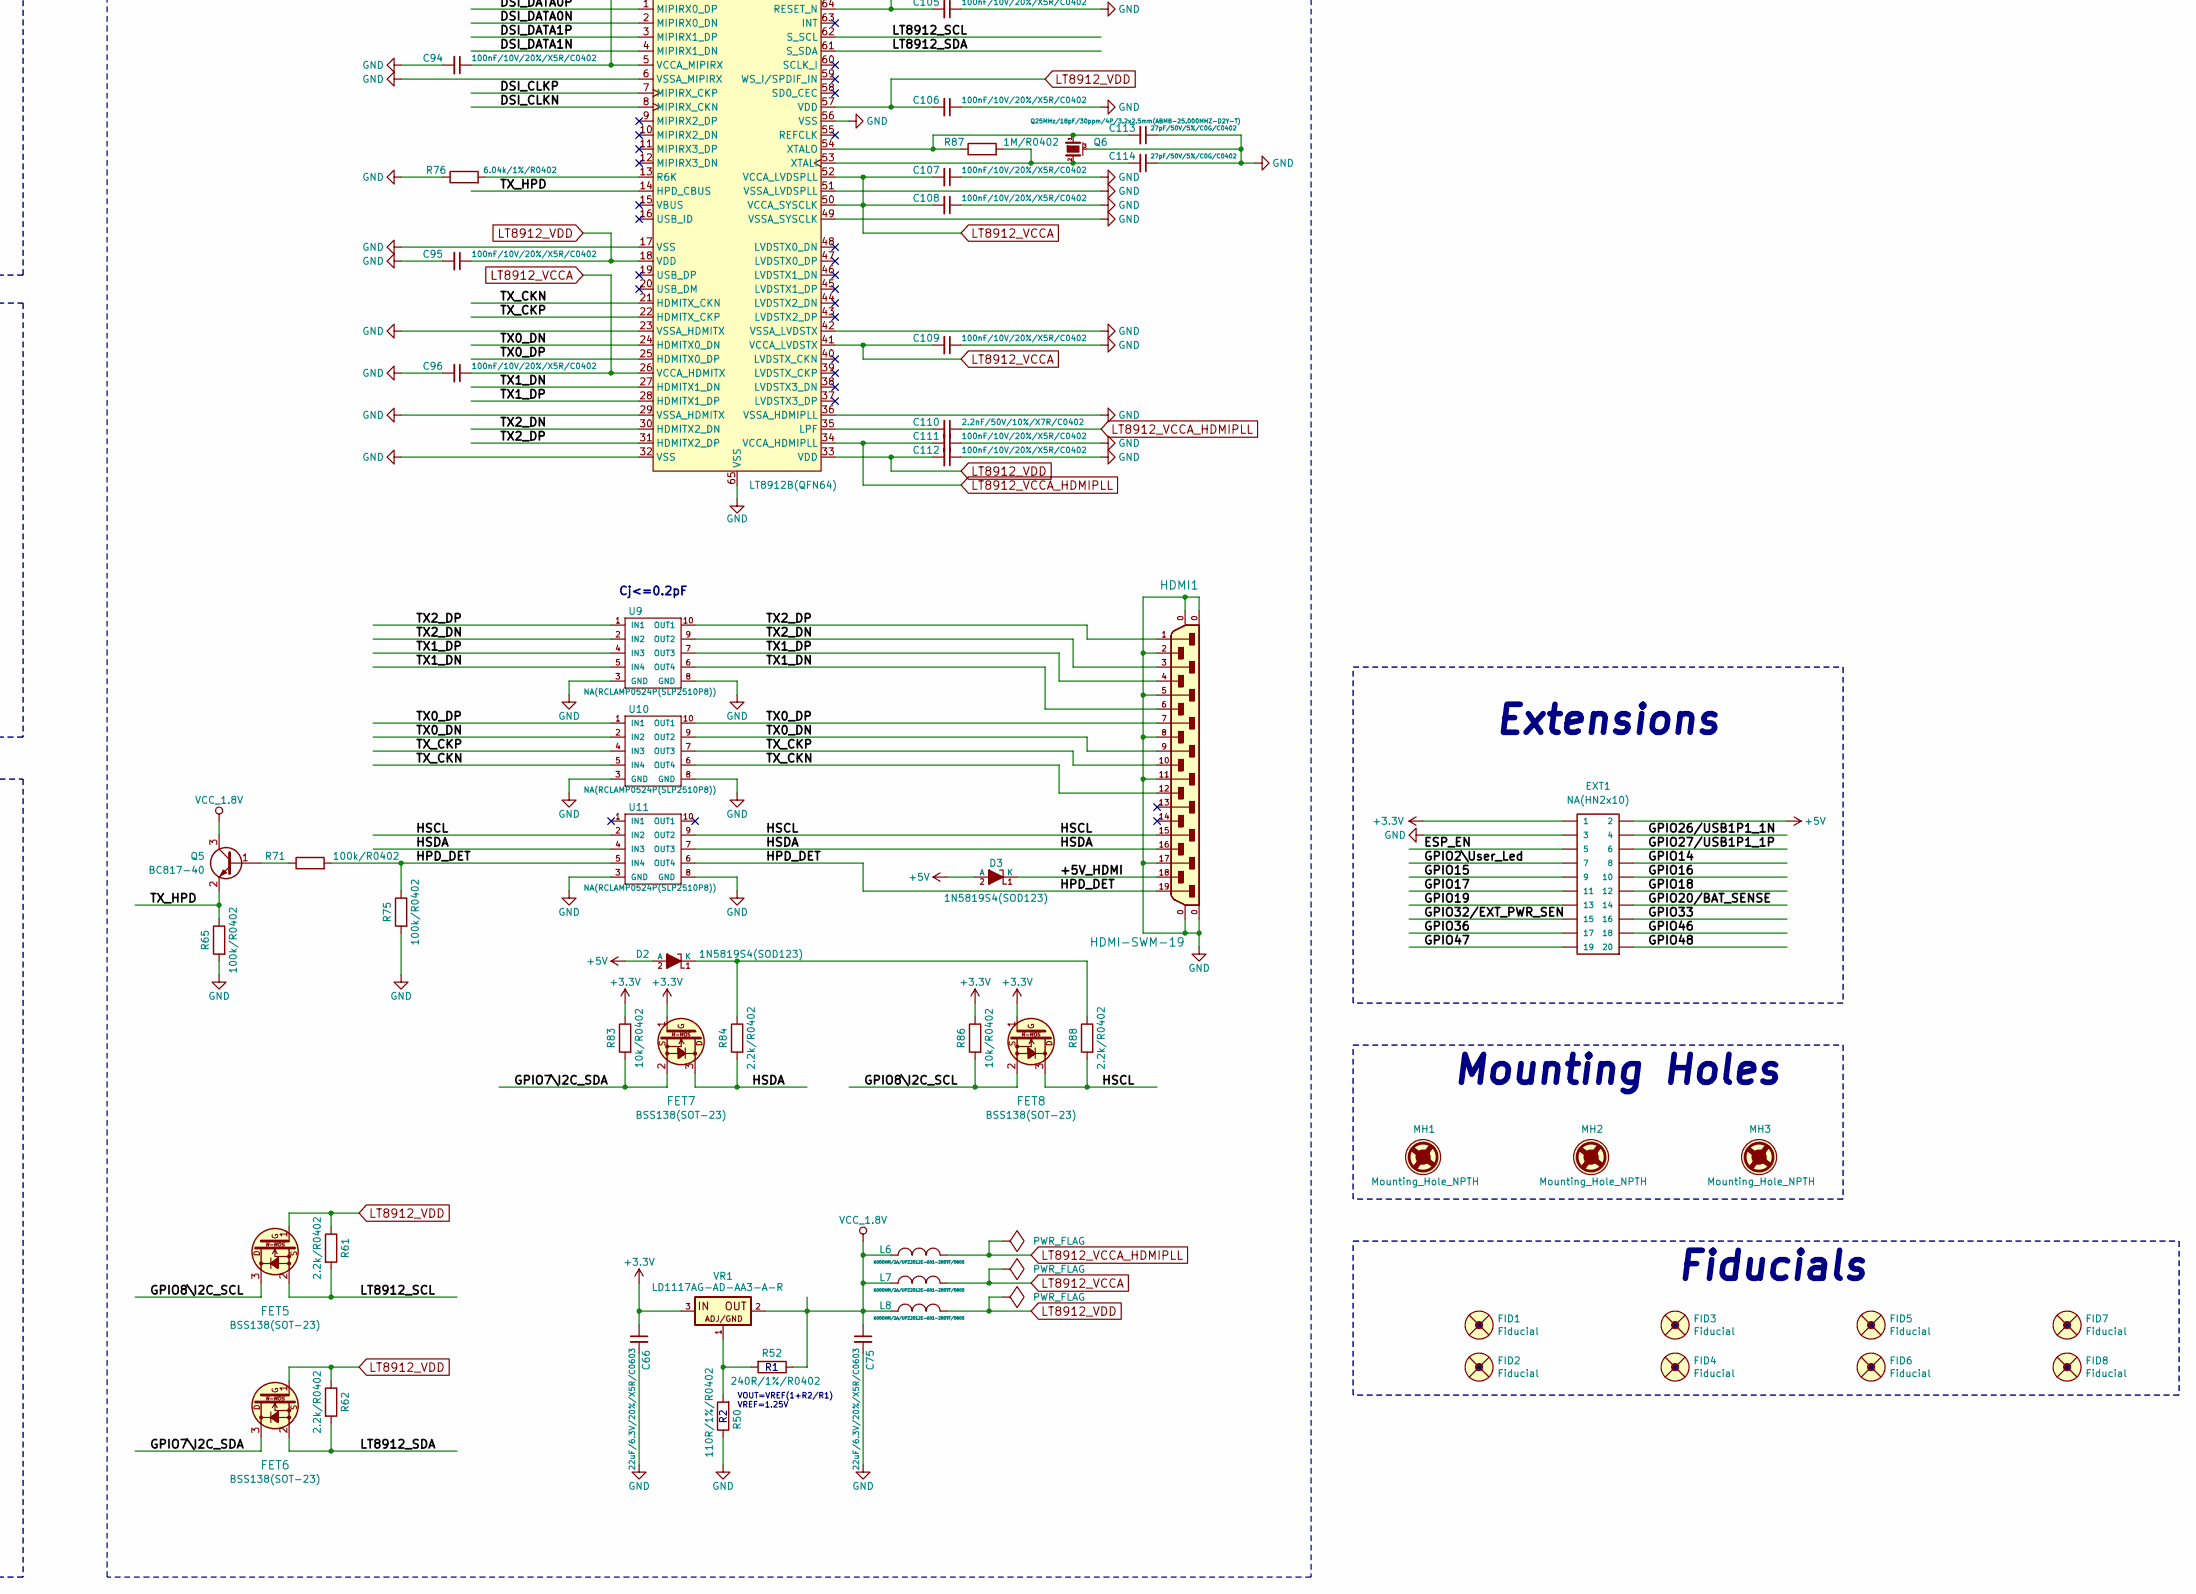
[picture p90: schematic ESP32-P4-PC_Rev_B.kicad_sch, part in row 2, column 2]

Parts:
3.3V1: TESTPAD; TESTPAD_40-ROUND
+5V1, +5V_EXT1, +5V_POE1, +5V_USB1: TESTPAD; TESTPAD_40-ROUND
ACT/SUS1: LED/RED/0603; LED_0603_KA
BAT1: PH2.0-2AT; PH2.0-2AT(BAT)
BAT_SENS_E1, BAT_SENS_E2: Opened; SJ_1_SMALLER
BOOT1: YTS-A016-X
C1, C2, C44, C45: 22pF/50V/5%/C0G/C0402; C_0402_5MIL_DWS
C3, C6, C18, C20, C22, C29, C41, C50, C56, C67, C68, C70, C76, C82, C99: 10uF/6.3V/20%/X5R/C0402; C_0402_5MIL_DWS
C4, C5, C7, C9, C11, C12, C19, C21, C23, C30, C31, C32, C38, C40, C42, C43, C46, C47, C49, C51, C52, C53, C54, C57, C69, C71, C85, C87, C91, C94, C95, C96, C101, C105, C106, C107, C108, C109, C111, C112, C115, C119, C120, C121, C128, C131: 100nF/10V/20%/X5R/C0402; C_0402_5MIL_DWS
C8, C10, C36, C39, C48, C55, C58, C61, C84, C86, C88, C97, C98, C100, C104, C126: 1uF/6.3V/10%/X5R/C0402; C_0402_5MIL_DWS
C13: 4.7uF/X5R/20%/10V/C0402; C_0402_5MIL_DWS
C14, C65, C74, C92, C93, C118, C129, C130, C132, C133, C134, C136: 47uF/6.3V/20%/X5R/C0805; C_0805_5MIL_DWS
C15, C16: 100nF/50V/20%/Y5V/C0603; C_0603_5MIL_DWS
C17: 1nF/2000V/10%/X7R/C1206; C_1206_5MIL_DWS_ISO
C24, C25, C79, C80, C81, C113, C114: 27pF/50V/5%/C0G/C0402; C_0402_5MIL_DWS
C26, C83: NA(10uF/6.3V/20%/X5R/C0402); C_0402_5MIL_DWS; not fitted
C27, C28: 150pF/50V/2%/NP0/C0402; C_0402_5MIL_DWS
C33: NA(100nF/10V/20%/X5R/C0402); C_0402_5MIL_DWS; not fitted
C34, C64, C122: NA(22uF/6.3V/20%/X5R/C0603); C_0603_5MIL_DWS; not fitted
C35, C37, C63, C66, C75, C102, C103, C123, C124: 22uF/6.3V/20%/X5R/C0603; C_0603_5MIL_DWS
C59, C62: NA(120pF/50V/5%/C0G/C0402); C_0402_5MIL_DWS; not fitted
C60: NA(100nF/10V/20%/X5R/C0402); C_0402_5MIL_DWS
C72, C73: NA(27pF/50V/5%/C0G/C0402); C_0402_5MIL_DWS; not fitted
C77, C78: 20pF/50V/5%/NP0/C0402; C_0402_5MIL_DWS
C89, C90, C116, C125, C127, C135: NA(47uF/6.3V/20%/X5R/C0805); C_0805_5MIL_DWS; not fitted
C110: 2.2nF/50V/10%/X7R/C0402; C_0402_5MIL_DWS
C117: 1000uF/10V/20%; CPOL-RM3.5mm_8.0x11.5mm_PTH
CHARGE1: LED/Yellow/0603; LED_0603_KA
CORE1: TESTPAD; TESTPAD_40-ROUND
D2, D3: 1N5819S4(SOD123); SOD-123_1C-2A_KA
D4: 1N5822/SS34/SMA; SMA-KA
DCDC_Vin1: Closed(1-2); SJ_2_SMALL_12_TIED
DC_VIN1: TESTPAD; TESTPAD_40-ROUND
EXT1: NA(HN2x10); HN2x10
FET1: IRLML6402(SOT-23); SOT23
FET3, FET4, FET5, FET6, FET7, FET8: BSS138(SOT-23); SOT23
FID1, FID3, FID5, FID7: Fiducial; Fiducial1x3
FID2, FID4, FID6, FID8: Fiducial; Fiducial1x3_Paste
GND1, GND2: TESTPAD; TESTPAD_40-ROUND
HDMI1: HDMI-SWM-19; HDMI-SWM-19_Paste
HEADSETS1: PJ-320D
L1, L2, L5, L6, L7, L8: 600OHM/2A/UPZ2012E-601-2R0TF/0805; L_0805_5MIL_DWS
L3, L4: 1.0uH/4.2A/DCR=35mR/20%/2.00x1.60x1.00mm/L2016(PI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; L_2016_MM
L9: NA(600OHM/2A/UPZ2012E-601-2R0TF/0805); L_0805_5MIL_DWS; not fitted
L11: 4.7uH/2.33A/DCR=70mR/20%/CD43(NRS4018T4R7MDGJ); CD42(43)
LAN1: RJP-003TC1(LPJ4112CNL)
LED_ACT1: LED/Yellow/0603; LED_0603_KA
LED_HOST1, LED_HOST2, LED_HOST3, LED_HOST4: LED/GREEN/0603; LED_0603_KA
LED_LINK1: LED/GREEN/0603; LED_0603_KA
MH1, MH2, MH3: Mounting_Hole_NPTH; Mounting_Hole_Drill-3.3mm_Clerance-7mm
MICRO_SD1: TFC-WPAPR-08-LF; TFC-WPAPR-08
MIPI-CSI1: FPA-VZA2-15-LF; TE_1-1734248-5
MIPI-DSI1: FPA-VZA2-15-LF; TE_1-1734248-5
POE_PWR1: PH2.0-4AT; PH2.0-4PLB
PWR1: LED/RED/0603; LED_0603_KA
PWR_SENS_E1: Opened; SJ_1_SMALLER
Q1: Q32.768kHz/12.5pF/2P/SMD1206; CM7V-T1A(Crystal_Package-1206_3.20x1.50x0.65mm)
Q2, Q6: Q25MHz/18pF/30ppm/4P/3.2x2.5mm(ABM8-25.000MHZ-D2Y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; TSX-3.2x2.5mm_GND(3)
Q3: Q40.000MHz/12pF/10ppm/4P/3.2x2.5x0.70mm(Harmony_E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; TSX-3.2x2.5mm_GND(3)
Q4: Q12MHz/18pF/30ppm/4P/3.2x2.5mm(ABM8-12.000MHZ-D2Y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; TSX-3.2x2.5mm_GND(3)
Q5: BC817-40; SOT23
R1, R2: 4.02k/1%/R0402; R_0402_5MIL_DWS
R3, R27, R41, R42, R43, R48, R54, R55, R64, R66, R67, R68, R70, R83, R85, R86, R102: 10k/R0402; R_0402_5MIL_DWS
R4, R8, R9, R39, R56, R57, R61, R62, R72, R73, R74, R80, R82, R84, R88, R91, R92, R93: 2.2k/R0402; R_0402_5MIL_DWS
R5, R6: 5.1k/1%/R0402; R_0402_5MIL_DWS
R7, R10, R11, R12, R21, R22, R33, R37, R49, R69: 4.7k/R0402; R_0402_5MIL_DWS
R13: 10M/R0402; R_0402_5MIL_DWS
R14, R15, R16, R25, R26, R38: 22R/R0402; R_0402_5MIL_DWS
R17: 6.19k/1%/R0402; R_0402_5MIL_DWS
R18, R28: NA(10k/R0402); R_0402_5MIL_DWS; not fitted
R19, R32, R63: NA/R0402; R_0402_5MIL_DWS; not fitted
R20: NA(10M/R0402); R_0402_5MIL_DWS; not fitted
R23: NA(4.7k/R0402); R_0402_5MIL_DWS; not fitted
R24, R105: 24.9k/1%/R0402; R_0402_5MIL_DWS
R29, R30: NA(2.2k/R0402); R_0402_5MIL_DWS; not fitted
R31: 0R/R0603; R_0603_5MIL_DWS
R34, R35: 1.5k/R0402; R_0402_5MIL_DWS
R36: 220k/R0402; R_0402_5MIL_DWS
R40: NA(0R/R0402); R_0402_5MIL_DWS; not fitted
R44: 30.1k/1%/R0402; R_0402_5MIL_DWS
R45: 6.49k/1%/R0402; R_0402_5MIL_DWS
R46, R47: 10.5k/1%/R0402; R_0402_5MIL_DWS
R50: 110R/1%/R0402; R_0402_5MIL_DWS
R51: 49.9k/1%/R0402; R_0402_5MIL_DWS
R52: 240R/1%/R0402; R_0402_5MIL_DWS
R53: 2.7k/1%/R0402; R_0402_5MIL_DWS
R58, R59, R60: 33R/R0402; R_0402_5MIL_DWS
R65, R71, R75: 100k/R0402; R_0402_5MIL_DWS
R76: 6.04k/1%/R0402; R_0402_5MIL_DWS
R77: 10R/R0402; R_0402_5MIL_DWS
R78: NA(200R/R0402); R_0402_5MIL_DWS
R79: 200R/R0402; R_0402_5MIL_DWS
R81: NA/R0402; R_0402_5MIL_DWS
R87: 1M/R0402; R_0402_5MIL_DWS
R89, R103: 6.81k/1%/R0402; R_0402_5MIL_DWS
R90, R94, R96: 470k/R0402; R_0402_5MIL_DWS
R95: 8.25k/1%/R0402; R_0402_5MIL_DWS
R98: 1.05k/1%/R0402; R_0402_5MIL_DWS
RM1: RMAT_(4x0402)_4.7k; RA0805_(4X0402)_xx_BIGGEROUTPADS
RM2: RA0805_(4X0402)_33R; RA0805_(4X0402)_xx_BIGGEROUTPADS
RST1: YTS-A016-X
TVS1: ESDS314DBVR(SOT-23-5); SOT-23-5
U1: ESP32-P4NRWxx(QFN104); QFN104_10mm×10mm_Pitch_0.35mm
U2: IP101GRR(32-PIN_QFN); QFN32_EP(33)_4.00x4.00x0.80mm_Pitch_0.40mm
U3: W25Q128JVSIQ(16MB); SO-8_208mil
U4, U5: TPS62A02ADRLR(SOT-563-6); SOT-563-6
U6: CH217K(SOT23-6L); SOT23-6
U7: FE1.1s(SSOP-28); SSOP28_10x4mm_Pitch_0.64mm
U8: ES8311(QFN-20); QFN-20_EP(21)_3x3x0.6mm_Pitch_0.4mm
U9, U10, U11: NA(RCLAMP0524P(SLP2510P8)); SLP2510P8_TEST
U12: LT8912B(QFN64); QFN64_7.5x7.5mm_Pitch_0.4mm
U13, U16: TPS2116; SOT-5X3
U14: MT3608(SOT23-6); SOT23-6
U15: TP4054-42-SOT25-R(SOT23-5); SOT-23-5
UEXT1: P-B-V-10-LF; GBH-254-SMT-10
USB-Serial/JTAG1: USB-C-16P-F(A40-00119-A52-12); USB2.0_TYPE-C(A40-00119-A52-12)_Paste
USB_HOST1-2, USB_HOST3-4: USBB1-FRWH-4A(USB-Ax2); USB_TWO_LEVEL
USER_LED1: LED/GREEN/0603; LED_0603_KA
VBAT1: TESTPAD; TESTPAD_40-ROUND
VO1, VO2, VO3, VO4: TESTPAD; TESTPAD_40-ROUND
VR1: LD1117AG-AD-AA3-A-R; SOT223
VR2: AP1231-3.3V(SOT23-5); SOT-23-5

Connections:
3.3V_PHY: C20.1, C21.1, C22.1, C23.1, L2.2, R7.2, R8.2, R18.1, R21.1, R22.1, R34.1, R35.1, R37.1, U2.13 (VDD_IO), U2.31 (AVDD33)
50MHz_CLKO: R38.2, U2.14 (RXCLK/50M_CLKO)
+1V8: C39.2, C54.2, C55.2, U1.59 (VDDPST), U1.67 (VDDPST), U1.72 (VFB2/VO2), VO2.1
+2.5V: C10.1, C11.1, C58.2, U1.41 (VDD_MIPI_DPHY), U1.73 (VFB3/VO3), VO3.1
+3.3V: 3.3V1.1, C3.1, C4.1, C5.2, C12.1, C13.1, C29.1, C30.1, C32.2, C41.2, C42.2, C43.2, C46.2, C50.2, C51.2, C53.2, C56.1, C57.1, C59.2, C63.1, C64.1, C66.1, DCDC_Vin1.3, EXT1.1, FET1.2, FET7.1 (G), FET8.1 (G), L2.1, L3.2, L9.1, MIPI-CSI1.15, MIPI-DSI1.14, MIPI-DSI1.15, R4.1, R27.1, R28.1, R29.1, R30.1, R33.2, R41.1, R42.1, R43.1, R44.2, R49.1, R83.1, R86.1, R92.2, R93.2, U1.9 (VDDPST_1), U1.21 (VDDPST_2), U1.51 (VCCA), U1.62 (VDDPST_4), U1.75 (VDDPST_LDO), U1.77 (VDDPST_DCDC), U1.96 (VDDPST_6), U1.101 (VDDA), U1.102 (VBAT), UEXT1.1, VR1.3 (IN)
+3.3VA: C82.1, FET3.1 (G), FET4.1 (G), L5.1, L9.2, R56.2, R57.2, R63.2, R68.1, R77.1, VR2.5 (VOUT)
+5V: +5V1.1, C67.1, C74.1, C76.1, C91.2, C122.1, C123.1, D2.2 (A), D3.2 (A), D4.1 (K), EXT1.2, R69.2, R95.1, U6.6 (VIN), U7.20 (V5), VR2.1 (VIN)
+5VP: +5V_POE1.1, C120.2, C134.2, C135.2, C136.2, POE_PWR1.4, U13.6 (VIN2)
+5V_EXT: +5V_EXT1.1, C31.2, C118.2, C125.1, C126.1, C130.1, C131.2, CHARGE1.2 (A), R36.1, R39.2, R105.2, U13.2 (VOUT), U13.7 (VOUT), U15.4 (VCC), U16.3 (VIN1), U16.5 (MODE)
+5V_HDMI: D3.1 (K), HDMI1.18
+5V_USB: +5V_USB1.1, C119.2, C127.2, C132.2, C133.2, R24.2, U13.3 (VIN1), U13.5 (MODE), USB-Serial/JTAG1.A4 (VBUS), USB-Serial/JTAG1.A9 (VBUS), USB-Serial/JTAG1.B4 (VBUS), USB-Serial/JTAG1.B9 (VBUS)
+5V_USB_HOST: C89.2, C90.2, C92.2, C93.2, U6.1 (VOUT), USB_HOST1-2.1.1, USB_HOST1-2.2.1, USB_HOST3-4.1.1, USB_HOST3-4.2.1
ADCVREF: C86.1, R79.2, U8.15 (ADCVREF)
CSI_CLKN: MIPI-CSI1.8, U1.45 (CSI_CLKN)
CSI_CLKP: MIPI-CSI1.9, U1.44 (CSI_CLKP)
CSI_DATA0N: MIPI-CSI1.2, U1.42 (CSI_DATAN0)
CSI_DATA0P: MIPI-CSI1.3, U1.43 (CSI_DATAP0)
CSI_DATA1N: MIPI-CSI1.5, U1.46 (CSI_DATAN1)
CSI_DATA1P: MIPI-CSI1.6, U1.47 (CSI_DATAP1)
CSI_IO0\Reset: MIPI-CSI1.11, R27.2
CSI_IO1\Strobe: MIPI-CSI1.12, R28.2
DCDC_VIN: C34.1, C35.1, C37.1, C116.2, C117.1 (+), C124.1, C128.2, DCDC_Vin1.1, DCDC_Vin1.2, DC_VIN1.1, L11.2, U4.3 (VIN), U4.4 (EN), U5.3 (VIN), U14.4 (EN), U14.5 (IN), U16.2 (VOUT), U16.7 (VOUT)
DSI_CLKN: MIPI-DSI1.5, U1.37 (DSI_CLKN), U12.8 (MIPIRX_CKN)
DSI_CLKP: MIPI-DSI1.6, U1.38 (DSI_CLKP), U12.7 (MIPIRX_CKP)
DSI_DATA0N: MIPI-DSI1.8, U1.40 (DSI_DATAN0), U12.2 (MIPIRX0_DN)
DSI_DATA0P: MIPI-DSI1.9, U1.39 (DSI_DATAP0), U12.1 (MIPIRX0_DP)
DSI_DATA1N: MIPI-DSI1.2, U1.36 (DSI_DATAN1), U12.4 (MIPIRX1_DN)
DSI_DATA1P: MIPI-DSI1.3, U1.35 (DSI_DATAP1), U12.3 (MIPIRX1_DP)
EN_DCDC: U1.79 (EN_DCDC), U5.4 (EN)
ESP_EN: C40.2, EXT1.5, R19.1, R41.2, RST1.1, U1.103 (CHIP_PU)
ESP_LDO_VO1: C8.2, C9.2, C36.1, C38.2, R48.1, U1.30 (VDDPST_3), U1.71 (VFB1/VO1), U3.8 (VCC), VO1.1
ESP_LDO_VO4: C48.1, C49.1, C61.2, R11.1, R12.1, RM1.1.2, RM1.2.2, RM1.3.2, RM1.4.2, U1.74 (VFB4/VO4), U1.85 (VDDPST_5), VO4.1
FB_DCDC: C62.1, R46.1, R47.1, U1.78 (FB_DCDC), U5.5 (FB)
FLASH_CK: U1.32 (FLASH_CK), U3.6 (CLK)
FLASH_CS: R48.2, U1.27 (FLASH_CS), U3.1 (#CS)
FLASH_D: U1.33 (FLASH_D), U3.5 (DI(IO0))
FLASH_HOLD: U1.31 (FLASH_HOLD), U3.7 (#HOLD(IO3))
FLASH_Q: U1.28 (FLASH_Q), U3.2 (DO(IO1))
FLASH_WP: U1.29 (FLASH_WP), U3.3 (#WP(IO2))
GND: ACT/SUS1.1 (K), BAT1.2, BOOT1.2, C1.1, C2.1, C3.2, C4.2, C5.1, C6.2, C7.2, C8.1, C9.1, C10.2, C11.2, C12.2, C13.2, C14.2, C15.1, C16.1, C17.1, C18.2, C19.2, C20.2, C21.2, C22.2, C23.2, C24.1, C25.1, C26.2, C27.2, C28.2, C29.2, C30.2, C31.1, C32.1, C33.1, C34.2, C35.2, C36.2, C37.2, C38.1, C39.1, C40.1, C41.1, C42.1, C43.1, C44.1, C45.1, C46.1, C47.1, C48.2, C49.2, C50.1, C51.1, C52.1, C53.1, C54.1, C55.1, C56.2, C57.2, C58.1, C60.2, C61.1, C63.2, C64.2, C65.2, C66.2, C67.2, C68.2, C69.2, C70.2, C71.2, C72.2, C73.2, C74.2, C75.2, C89.1, C90.1, C91.1, C92.1, C93.1, C94.2, C95.2, C96.2, C105.1, C106.1, C107.1, C108.1, C109.1, C111.1, C112.1, C113.1, C114.1, C115.1, C116.1, C117.2 (-), C118.1, C119.1, C120.1, C121.1, C122.2, C123.2, C124.2, C125.2, C126.2, C127.1, C128.1, C129.1, C130.2, C131.1, C132.1, C133.1, C134.1, C135.1, C136.1, EXT1.3, GND1.1, GND2.1, HDMI1.0 (20), HDMI1.2, HDMI1.5, HDMI1.8, HDMI1.11, HDMI1.17, LAN1.7 (GND/NC), LAN1.8 (NC/GND), LED_LINK1.1 (K), MICRO_SD1.6 (VSS), MICRO_SD1.10, MICRO_SD1.11, MICRO_SD1.12, MICRO_SD1.13, MIPI-CSI1.1, MIPI-CSI1.4, MIPI-CSI1.7, MIPI-CSI1.10, MIPI-DSI1.1, MIPI-DSI1.4, MIPI-DSI1.7, MIPI-DSI1.10, MIPI-DSI1.13, POE_PWR1.3, PWR1.1 (K), Q2.3 (case), Q3.3 (case), Q4.3 (case), Q6.3 (case), R1.2, R2.2, R3.1, R5.1, R6.1, R10.1, R17.2, R23.1, R31.1, R45.2, R47.2, R50.1, R51.1, R53.1, R65.2, R70.2, R75.2, R76.1, R89.2, R94.2, R96.2, R98.2, R102.2, R103.2, RST1.2, TVS1.2 (GND), U1.105 (GND), U2.1 (TXER/FXSD), U2.33 (GND), U3.4 (GND), U4.1 (GND), U5.1 (GND), U6.2 (GND), U7.1 (GND), U9.3 (GND), U9.8 (GND), U10.3 (GND), U10.8 (GND), U11.3 (GND), U11.8 (GND), U12.6 (VSSA_MIPIRX), U12.17 (VSS), U12.23 (VSSA_HDMITX), U12.29 (VSSA_HDMITX), U12.32 (VSS), U12.36 (VSSA_HDMIPLL), U12.42 (VSSA_LVDSTX), U12.49 (VSSA_SYSCLK), U12.51 (VSSA_LVDSPLL), U12.56 (VSS), U12.65 (VSS), U13.1 (GND), U14.2 (GND), U15.2 (GND), U16.1 (GND), UEXT1.2, USB-Serial/JTAG1.0 (SHELL), USB-Serial/JTAG1.A1 (GND), USB-Serial/JTAG1.A12 (GND), USB-Serial/JTAG1.B1 (GND), USB-Serial/JTAG1.B12 (GND), USB_HOST1-2.0, USB_HOST1-2.1.4, USB_HOST1-2.2.4, USB_HOST3-4.0, USB_HOST3-4.1.4, USB_HOST3-4.2.4
GNDA: C76.2, C77.2, C78.2, C79.2, C80.2, C81.2, C82.2, C83.2, C84.2, C85.2, C86.2, C87.2, C88.2, C99.2, C100.2, C101.1, C104.2, HEADSETS1.2, R31.2, R64.2, R68.2, R81.1, U8.5 (DGND), U8.10 (AGND), U8.21 (GND_EP), VR2.2 (VSS)
GPIO2\User_Led: EXT1.7, U1.2 (GPIO2/TOUCH_0/MTCK), USER_LED1.1 (K)
GPIO3\SD_DET: R12.2, R16.1, U1.3 (GPIO3/TOUCH_1/MTDI)
GPIO4\SPI_SCK(CLK): U1.4 (GPIO4/TOUCH_2/MTMS), UEXT1.9
GPIO5\SPI_CSn(CS#): U1.5 (GPIO5/TOUCH_3/MTDO), UEXT1.10
GPIO6\CODEC_PWR_DIS#: R49.2, U1.6 (GPIO6/TOUCH_4/GPSPI_SPI2_HOLD), VR2.3 (CE)
GPIO7\I2C_SDA: FET3.3 (D), FET6.3 (D), FET7.2 (S), MIPI-CSI1.14, MIPI-DSI1.12, R30.2, R83.2, U1.7 (GPIO7/TOUCH_5/GPSPI_SPI2_CS)
GPIO8\I2C_SCL: FET4.3 (D), FET5.3 (D), FET8.2 (S), MIPI-CSI1.13, MIPI-DSI1.11, R29.2, R86.2, U1.8 (GPIO8/TOUCH_6/GPSPI_SPI2_D/UART0_RTS)
GPIO9\I2S_DSDIN: RM2.4.1, U1.10 (GPIO9/TOUCH_7/GPSPI_SPI2_CK/UART0_CTS)
GPIO10\I2S_LRCK: RM2.3.1, U1.11 (GPIO10/TOUCH_8/GPSPI_SPI2_Q/UART1_TXD)
GPIO11\I2S_ASDOUT: RM2.2.1, U1.12 (GPIO11/TOUCH_9/GPSPI_SPI2_WP/UART1_RTD)
GPIO12\I2S_SCLK: RM2.1.1, U1.13 (GPIO12/TOUCH_10/UART1_RTS)
GPIO13\I2S_MCLK: R60.2, U1.14 (GPIO13/TOUCH_11/UART0_CTS)
GPIO14: EXT1.8, U1.15 (GPIO14/TOUCH_12/LP_UART_TXD)
GPIO15: EXT1.9, U1.16 (GPIO15/TOUCH_13/LP_UART_RXD)
GPIO16: EXT1.10, U1.17 (GPIO16/ADC0)
GPIO17: EXT1.11, U1.18 (GPIO17/ADC1)
GPIO18: EXT1.12, U1.19 (GPIO18/ADC2)
GPIO19: EXT1.13, U1.20 (GPIO19/ADC3)
GPIO20/BAT_SENSE: BAT_SENS_E1.2, EXT1.14, U1.22 (GPIO20/ADC4)
GPIO21/HUB_RST#: R54.2, U1.23 (GPIO21/ADC5), U7.17 (XRSTJ)
GPIO22/I2C_SDA2: R93.1, U1.24 (GPIO22/ADC6/DBG_PSRAM_CK), UEXT1.6
GPIO23/I2C_SCL2: R92.1, U1.25 (GPIO23/ADC7/50MHz_ref_clk_out/DBG_PSRAM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), UEXT1.5
GPIO26/USB1P1_1N: EXT1.4, U1.55 (GPIO26/USB1P1_N1)
GPIO27/USB1P1_1P: EXT1.6, U1.56 (GPIO27/USB1P1_P1)
GPIO32/EXT_PWR_SEN: EXT1.15, PWR_SENS_E1.2, U1.63 (GPIO32/I3CMST_SCL/GPSPI_SPI2_HOLD/EMAC_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)
GPIO33: EXT1.16, U1.64 (GPIO33/I3CMST_SDA/GPSPI_SPI2_WP/EMAC_PH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)
GPIO34\RMII_TXD0: U1.65 (GPIO34/GPSPI_SPI2_IO4/EMAC_PHY_TXD0/DBG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), U2.9 (TXD0)
GPIO35\RMII_TXD1: BOOT1.1, C60.1, R43.2, U1.66 (GPIO35/GPSPI_SPI2_IO5/EMAC_PHY_TXD1/DBG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), U2.8 (TXD1)
GPIO36: EXT1.17, R42.2, U1.68 (GPIO36/GPSPI_SPI2_IO6/EMAC_PHY_TXER/DBG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)
GPIO46: EXT1.18, U1.88 (GPIO46/SD1_DATA5/EMAC_PHY_RXD0/DBG_PSRA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)
GPIO47: EXT1.19, U1.89 (GPIO47/SD1_DATA6/EMAC_PHY_RXD1/DBG_PSRA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)
GPIO48: EXT1.20, U1.90 (GPIO48/SD1_DATA7/EMAC_PHY_RXER)
GPIO53\SPI_TX(MOSI): U1.97 (GPIO53/ADC12/EMAC_PHY_RXD1/DBG_FLASH_CK), UEXT1.8
GPIO54\SPI_RX(MISO): U1.98 (GPIO54/ADC13/EMAC_PHY_RXER/DBG_FLASH_D), UEXT1.7
HP-L: C103.1, HEADSETS1.4
HP-R: C102.1, HEADSETS1.3
HPD_DET: HDMI1.19, R71.2, R75.1, U11.5 (IN4), U11.6 (OUT4)
HSCL: FET8.3 (D), HDMI1.15, R88.2, U11.2 (IN2), U11.9 (OUT2)
HSDA: FET7.3 (D), HDMI1.16, R84.2, U11.4 (IN3), U11.7 (OUT3)
HUB_DRV: LED_HOST1.2 (A), LED_HOST2.2 (A), LED_HOST3.1 (K), LED_HOST4.1 (K), R74.1, U7.22 (DRV)
HUB_LED1: R72.1, U7.23 (LED1/SCL)
HUB_LED2: R73.1, U7.24 (LED2)
LAN_Shield: C17.2, LAN1.0 (Shield)
LED0\PHY_AD0: LED_ACT1.1 (K), R7.1, U2.11 (LED0/PHY_AD0)
LED3\PHY_AD3: R9.2, R10.2, U2.12 (LED3/PHY_AD3)
LT8912_SCL: FET5.2 (S), R61.2, U12.62 (S_SCL)
LT8912_SDA: FET6.2 (S), R62.2, U12.61 (S_SDA)
LT8912_VCCA: C94.1, C96.1, C107.2, C108.2, C109.2, L7.2, U12.5 (VCCA_MIPIRX), U12.26 (VCCA_HDMITX), U12.41 (VCCA_LVDSTX), U12.50 (VCCA_SYSCLK), U12.52 (VCCA_LVDSPLL)
LT8912_VCCA_HDMIPLL: C110.1, C111.2, L6.2, U12.34 (VCCA_HDMIPLL)
LT8912_VDD: C95.1, C106.2, C112.2, FET5.1 (G), FET6.1 (G), L8.2, R61.1, R62.1, R85.2, U12.18 (VDD), U12.33 (VDD), U12.57 (VDD)
LX2: D4.2 (A), L11.1, U14.1 (LX)
MDC: R34.2, U1.61 (GPIO31/GPSPI_SPI2_Q/EMAC_PHY_RXER/DBG_P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), U2.22 (MDC)
MDIO: R35.2, U1.95 (GPIO52/ADC11/EMAC_PHY_RXD0/DBG_FLASH_HO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), U2.23 (MDIO)
MICN: C97.1, R80.2, R81.2
MICP: C98.1, HEADSETS1.1, R82.2
unnamed: ACT/SUS1.2 (A), R74.2
unnamed: BAT_SENS_E1.1, C115.2, R90.2, R96.1
unnamed: BAT_SENS_E2.1, R90.1
unnamed: C1.2, Q1.1, R13.1, U1.104 (GPIO0/XTAL_32K_N)
unnamed: C2.2, Q1.2, R13.2, U1.1 (GPIO1/XTAL_32K_P)
unnamed: C15.2, LAN1.4 (TCT)
unnamed: C16.2, LAN1.5 (RCT)
unnamed: C18.1, C19.1, U2.28 (REGOUT)
unnamed: C24.2, Q2.1, R20.2, U2.2 (X1)
unnamed: C25.2, Q2.2, R20.1, U2.3 (X2)
unnamed: C33.2, R40.2, U1.54 (NC(VDD_HP_1))
unnamed: C44.2, Q3.1, R32.1, U1.100 (XTAL_P)
unnamed: C45.2, Q3.2, R32.2, U1.99 (XTAL_N)
unnamed: C59.1, R44.1, R45.1, U4.5 (FB)
unnamed: C72.1, Q4.1, U7.3 (XI)
unnamed: C73.1, Q4.2, U7.2 (XO)
unnamed: C77.1, R56.1, R58.1, U8.1 (CCLK/SCL)
unnamed: C78.1, R57.1, R59.1, U8.19 (CDATA/SDA)
unnamed: C79.1, RM2.3.2, U8.8 (LRCK)
unnamed: C80.1, RM2.1.2, U8.6 (SCLK/DMIC_SCL)
unnamed: C81.1, R60.1, U8.2 (MCLK)
unnamed: C83.1, C85.1, C87.1, L5.2, U8.3 (PVDD), U8.4 (DVDD)
unnamed: C84.1, U8.16 (VMID)
unnamed: C88.1, U8.14 (DACVREF)
unnamed: C97.2, U8.17 (MIC1N)
unnamed: C98.2, U8.18 (MIC1P/DMIC_SDA)
unnamed: C99.1, C100.1, C101.2, R77.2, R78.2, U8.11 (AVDD)
unnamed: C102.2, U8.13 (OUTN)
unnamed: C103.2, U8.12 (OUTP)
unnamed: C104.1, R78.1, R79.1, R80.1, R82.1
unnamed: C105.2, R85.1, U12.64 (RESET_N)
unnamed: C110.2, U12.35 (LPF)
unnamed: C113.2, Q6.1, R87.1, U12.54 (XTALO)
unnamed: C114.2, Q6.2, R87.2, U12.53 (XTALI)
unnamed: CHARGE1.1 (K), R91.1
unnamed: D2.1 (K), R84.1, R88.1
unnamed: FET3.2 (S), R59.2
unnamed: FET4.2 (S), R58.2
unnamed: L4.1, U5.2 (SW)
unnamed: LED_ACT1.2 (A), R8.1
unnamed: LED_HOST1.1 (K), LED_HOST3.2 (A), R72.2
unnamed: LED_HOST2.1 (K), LED_HOST4.2 (A), R73.2
unnamed: LED_LINK1.2 (A), R9.1
unnamed: MICRO_SD1.9, R16.2
unnamed: PWR1.2 (A), R39.1
unnamed: PWR_SENS_E1.1, R36.2, R94.1
unnamed: Q5.1 (B), R71.1
unnamed: R1.1, U1.34 (DSI_REXT)
unnamed: R2.1, U1.48 (CSI_REXT)
unnamed: R4.2, USER_LED1.2 (A)
unnamed: R5.2, USB-Serial/JTAG1.B5 (CC2)
unnamed: R6.2, USB-Serial/JTAG1.A5 (CC1)
unnamed: R17.1, U2.25 (ISET)
unnamed: R21.2, U2.4 (COL/RMII)
unnamed: R22.2, R23.2, U2.20 (CRS/LEDMOD)
unnamed: R24.1, R89.1, U13.4 (PR1)
unnamed: R50.2, R52.2, VR1.1 (ADJ/GND)
unnamed: R51.2, U6.5 (ISET)
unnamed: R53.2, U7.14 (REXT)
unnamed: R55.2, U7.19 (BUSJ)
unnamed: R63.1, R64.1, U8.20 (CE/AD0)
unnamed: R69.1, R70.1, U7.18 (VBUSM)
unnamed: R76.2, U12.13 (R6K)
unnamed: R91.2, U15.1 (CHRGb)
unnamed: R95.2, R98.1, U14.3 (FB)
unnamed: R102.1, U15.5 (PROG)
unnamed: R103.1, R105.1, U16.4 (PR1)
unnamed: RM2.2.2, U8.7 (ASDOUT)
unnamed: RM2.4.2, U8.9 (DSDIN)
OVCUR#: R67.1, U6.3 (FLAG#), U7.26 (OVCJ)
PG_Core: U5.6 (PG)
PHY_RSTN: C26.1, R18.2, R19.2, U1.94 (GPIO51/ADC10/EMAC_PHY_RXDV/DBG_FLASH_WP), U2.32 (RESET_N)
PW+: LAN1.9 (PW+), POE_PWR1.2
PW-: LAN1.10 (PW-), POE_PWR1.1
PWREN#: R66.1, U6.4 (EN#), U7.25 (PWRJ)
RD+: LAN1.3 (RD+), TVS1.5 (I/O4), U2.27 (MDI_RP)
RD-: LAN1.6 (RD-), TVS1.1 (I/O1), U2.26 (MDI_RN)
RMII_CLK: R38.1, U1.93 (GPIO50/ADC9/EMAC_RMII_CLK/DBG_FLASH_Q), U2.10 (TXCLK/50M_CLKI)
RMII_RXD0: U1.58 (GPIO29/GPSPI_SPI2_D/EMAC_PHY_RXD0/DBG_P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), U2.18 (RXD0)
RMII_RXD1: U1.60 (GPIO30/GPSPI_SPI2_CK/EMAC_PHY_RXD1/DBG_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), U2.17 (RXD1)
RMII_RXDV: U1.57 (GPIO28/GPSPI_SPI2_CS/EMAC_PHY_RXDV/DBG_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), U2.19 (RXDV/CRS_DV/FX_HEN)
RMII_TXEN: U1.92 (GPIO49/ADC8/EMAC_PHY_TXEN/DBG_FLASH_CS), U2.5 (TXEN)
RXER/INTR_32: R37.2, U2.21 (RXER/INTR_32)
SD1_CLK: MICRO_SD1.5 (CLK/SCLK), U1.84 (GPIO43/SD1_CLK/EMAC_PHY_TXER/DBG_PSRAM_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)
SD1_CMD: MICRO_SD1.3 (CMD/DI), R11.2, U1.86 (GPIO44/SD1_CMD/EMAC_RMII_CLK/DBG_PSRAM_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)
SD1_D0: MICRO_SD1.7 (DAT0/DO), RM1.4.1, U1.80 (GPIO39/SD1_CDATA0/reference_clock_of_50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)
SD1_D1: MICRO_SD1.8 (DAT1/RES), RM1.3.1, U1.81 (GPIO40/SD1_CDATA1/EMAC_PHY_TXEN/DBG_PSR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)
SD1_D2: MICRO_SD1.1 (DAT2/RES), RM1.2.1, U1.82 (GPIO41/SD1_CDATA2/EMAC_PHY_TXD0/DBG_PSR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)
SD1_D3: MICRO_SD1.2 (CD/DAT3/CS), RM1.1.1, U1.83 (GPIO42/SD1_CDATA3/EMAC_PHY_TXD1/DBG_PSR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)
SD1_PWR_EN: FET1.1, R3.2, U1.87 (GPIO45/SD1_DATA4/EMAC_PHY_RXDV/DBG_PSRA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)
SD1_VDD: C14.1, L1.2, MICRO_SD1.4 (VDD)
SW1: L3.1, U4.2 (SW)
TD+: LAN1.1 (TD+), TVS1.4 (I/O3), U2.30 (MDI_TP)
TD-: LAN1.2 (TD-), TVS1.3 (I/O2), U2.29 (MDI_TN)
TX0_DN: HDMI1.9, U10.2 (IN2), U10.9 (OUT2), U12.24 (HDMITX0_DN)
TX0_DP: HDMI1.7, U10.1 (IN1), U10.10 (OUT1), U12.25 (HDMITX0_DP)
TX1_DN: HDMI1.6, U9.5 (IN4), U9.6 (OUT4), U12.27 (HDMITX1_DN)
TX1_DP: HDMI1.4, U9.4 (IN3), U9.7 (OUT3), U12.28 (HDMITX1_DP)
TX2_DN: HDMI1.3, U9.2 (IN2), U9.9 (OUT2), U12.30 (HDMITX2_DN)
TX2_DP: HDMI1.1, U9.1 (IN1), U9.10 (OUT1), U12.31 (HDMITX2_DP)
TX_CKN: HDMI1.12, U10.5 (IN4), U10.6 (OUT4), U12.21 (HDMITX_CKN)
TX_CKP: HDMI1.10, U10.4 (IN3), U10.7 (OUT3), U12.22 (HDMITX_CKP)
TX_HPD: Q5.2 (E), R65.1, U12.14 (HPD_CBUS)
UART0_RX: R33.1, U1.70 (GPIO38/UART0_RXD/GPSPI_SPI2_DQS), UEXT1.4
UART0_TX: U1.69 (GPIO37/UART0_TXD/GPSPI_SPI2_IO7), UEXT1.3
USB1P1_0+: R25.2, U1.53 (GPIO25/USB1P1_P0)
USB1P1_0-: R26.2, U1.52 (GPIO24/USB1P1_N0)
USB1P1_0N: C27.1, R26.1, USB-Serial/JTAG1.A7 (DN1), USB-Serial/JTAG1.B7 (DN2)
USB1P1_0P: C28.1, R25.1, USB-Serial/JTAG1.A6 (DP1), USB-Serial/JTAG1.B6 (DP2)
USB_D1+: U7.11 (DP1), USB_HOST1-2.1.3
USB_D1-: U7.10 (DM1), USB_HOST1-2.1.2
USB_D2+: U7.9 (DP2), USB_HOST1-2.2.3
USB_D2-: U7.8 (DM2), USB_HOST1-2.2.2
USB_D3+: U7.7 (DP3), USB_HOST3-4.1.3
USB_D3-: U7.6 (DM3), USB_HOST3-4.1.2
USB_D4+: U7.5 (DP4), USB_HOST3-4.2.3
USB_D4-: U7.4 (DM4), USB_HOST3-4.2.2
USB_D+: R15.1, U1.50 (DP)
USB_D-: R14.1, U1.49 (DM)
USB_DN: R14.2, U7.15 (DMU)
USB_DP: R15.2, U7.16 (DPU)
VBAT: BAT1.1, BAT_SENS_E2.2, C121.2, C129.2, U15.3 (VBAT), U16.6 (VIN2), VBAT1.1
VCC_1.8V: C75.1, L6.1, L7.1, L8.1, Q5.3 (C), R52.1, VR1.2 (OUT)
VD18_O: C70.1, C71.1, U7.12 (VD18_O), U7.28 (VD18)
VD33_O: C68.1, C69.1, R54.1, R55.1, R66.2, R67.2, U7.13 (VD33), U7.21 (VD33_O)
VDD_CORE: C6.1, C7.1, C47.2, C52.2, C62.2, C65.1, CORE1.1, L4.2, R40.1, R46.2, U1.26 (VDD_HP_0), U1.76 (VDD_HP_2), U1.91 (VDD_HP_3)
VDD_SD: FET1.3, L1.1

Notes on the sheet:
One LDO is recommended to provide power supply to ES8311 because ES8311 is an analog device which will be sensitive to noise.
Cj<=0.2pF
XRSTJ - External Reset For normal applications, it should be pull-up to 3.3V.
Note: VFB/VO1: External power supply pin, outputting 0.1A current W25Q128JVSIQ max current consumption: 25mA
TXER/FXSD Transmit Error or FXSD. Type I(PD).
USB-to-serial converter and USB-to-JTAG (The pin functions of USB_DN and USB_DP are interchangeable. GPIO24/25 and GPIO26/27 are the D+ and D- pins of two USB PHY. USB Serial/JTAG can use any one of them, and the default one is GPIO24/25)
Power Supply
Ilim=1.20A
The termal pad must be connected to audio ground.
Vout=0.6*(1+Ra/Rb)
Two pull up resistors are recommended to I2C bus. R-C low pass filter is strongly recommended to I2C bus. The I2C route must be shielded by ground.
I2S/PCM digital serial audio port with Master or Slave mode.
The two FETs prevent powering the Codec when its power supply is disabled.
Note 4: This capacitors should be located as close to ES8311 package as possible.
REXT - External Bias Resistor. A 2.7KΩ (± 1%) resistor should be connected to VSS to provide internal bias reference.
See: Note 1
Boot Strapping Pins
Mounting Holes
LED0 -> Link/ACT: Active indicates the link has established, and blinking while TX/RX events occur
Over Current Indicator (Input, 5V-Tolerant), active low, for Global Over-Current Protection. VIL=-0.3~0.8V, VIH=2.0~5.5V
RXER/INTR_32 1: INTR function (default) 0: RXER function
COL/RMII 0: MII Mode 1: RMII Mode (default)
This pin TXER must be either floating or connecting to GND in RMII mode.
The transfer rate of I2C can be up to 400 kbps
RXDV/CRS_DV/FX_HEN: Receive Data Valid or Media Type Selection. Type I(PD). In RMII mode, this pin indicates the Carrier Sense and Receive Data Valid function.
TXER/FXSD 1: FXSD 0: TXER (default)
3.7V LI-PO Battery Connector
FE1.1s is USB 2.0 HIGH SPEED 4-PORT HUB CONTROLLER
TEST_ON 1: Enable Test mode. NC: Normal operation (default)
Ethernet PHY
The CH217K's FLAG# pin can generate an over-current or over-temperature alarm signal to notify the HUB controller and the computer, and the CH334/5 has built-in pull-up resistors.
LiPo Charger
See: Note 4
Test Mode Enable (I/O), active low with internal pull-up, and external Serial EEPROM Data/Address.
Test Enable: Set this pin to high to enable Test mode. Type I(PD).
High-performance MCU with RISC-V single-core and dual-core microprocessors Powerful image and voice processing capability 16 MB or 32 MB PSRAM in the chip's package 55 GPIOs, rich set of peripherals QFN104 (10×10 mm) Package
USB 2.0 OTG high-speed interface (DM/DP)
AUDIO
If a 50MHz clock is applied to pin10 TXCLK/50M_CLKI, X1 must be connected to GND.
1V8/3V3(Flash)
X2, Type O
Rset
PoE RJ45 Connector
Vout=0.6*(1+Rc/Rd)
USB-HUB
MIPI-CSI Camera & MIPI-DSI LCD
Codec
Raspberry Pi 1,2,3 and 4 Compatible! Replace for the TE's 1-1734248-5.
RESET_N: Enable a low status signal will reset the chip. Type I(PU).
Note 3: recommend VDDP and VDDD power supply turn on or off within 10 ms of each other; VDDD must be on when VDDA is on.
USB 2.0 OTG full-speed (The pin functions of USB_DN and USB_DP are interchangeable. GPIO24/25 and GPIO26/27 are the D+ and D- pins of two USB PHY. USB 2.0 OTG can use any one of them, and the default one is GPIO26/27)
The Seven-bit Chip Address must be: 0011 00x where "x" equals CE(input pin: 1 being connected to supply and 0 being connected to ground). Then, in hex format: 0x18
Flash
The VBUS Monitor (Input, 5V-Tolerant) of upstream facing port.
Buttons
External Power Sense
DMIC is supported only in master mode.
Extensions
1V1~1V3(Core) Default: 1V2
Option for Ferrite Bead
2V5(MIPI)
Voltage & Polarity!!!
Close to the PHY!
ESP32-P4
UEXT
VOUT=VREF(1+R2/R1) VREF=1.25V
Audio Codec Power Supply Enable/Disable Control.
Note 1: If the lenght of I2S Clock is larger than 10cm, please use 30pF capacitors between I2S clock route and ground!
SD/MMC Card
Rprog
Note: VFB/VO4: External power supply pin, outputting 0.2A current. The power consumption of microSD cards varies by manufacturer, but appears to be in the range of 66-330 mW (20-100 mA at a supply voltage of 3.3 V). Specifications from TwinMos technologies list a maximum of 149 mW (45 mA) during tr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
FE1.1s POWER CONSUMPTION: I_suspend = 800uA Icc(4x High-Speed) = 84mA
VDDIO(1.8V/3.3V)
Upstream facing port supports HighSpeed (480MHz) and Full-Speed (12MHz) modes; 4 downstream facing ports support High-Speed (480MHz), Full-Speed (12MHz), and Low-Speed (1.5MHz) modes;
I(Bat)
Single Port 10/100 MII/RMII/TP/Fiber Fast Ethernet Transceiver
1.1V Typical
1V8(PSRAM)
Note 2: Filter and decoupling capacitors should be located as close to ES8311 package as possible during layout.
VDD_SD_CARD(1V8/3V3(SDIO))
HDMI
Ilim(A)=60K/Rset
Notes related to TP4054-42-SOT25-R: 1. It's recommended VCC range is: (4.0~9.0)V 2. For the Programming Charge Current I(Bat) there are two equations: When I(Bat)≤0.15A, then: I(Bat) = 1000/Rprog = 100mA When I(Bat)>0.15A, then: Rprog = 1000/I(Bat)*(1.2-4/3*I(Bat))
Battery Measurement
USB-Serial/ JTAG
LED3 -> 100BT: Active indicates 100Mbps connection has established
PHY Address 0b(0xx1)
PWRJ - Power Enable Output (OD) This is an active low, open-drain output signal. Downstream Device Power Enable (Output), active low, for Ganged Power Switching.
CRS/LEDMOD 1: LED mode 2 (default) 0: LED mode 1
Bus power indicator: 0 - Bus Powered; 1 - Self Powered; (Input, 5V-Tolerant)
Integrated 12MHz Oscillator with feedback resistor, and crystal load capacitance; Load capacitance: 16pF ~ 20pF
X1, Type I
Fiducials
