OLIMEX/ESP32-P4-PC/SOFTWARE/ESP-IDF/p4_production_test/components/esp-bsp/components/esp_lvgl_port/examples/rgb_lcd/main/main.c

/*
 * SPDX-FileCopyrightText: 2022-2025 Espressif Systems (Shanghai) CO LTD
 *
 * SPDX-License-Identifier: Apache-2.0
 */

#include "esp_err.h"
#include "esp_log.h"
#include "esp_check.h"
#include "esp_idf_version.h"
#include "driver/i2c_master.h"
#include "esp_lcd_panel_io.h"
#include "esp_lcd_panel_ops.h"
#include "esp_lcd_panel_rgb.h"
#include "esp_lvgl_port.h"
#include "lv_demos.h"

#include "esp_lcd_touch_gt1151.h"

/* LCD size */
#define EXAMPLE_LCD_H_RES   (800)
#define EXAMPLE_LCD_V_RES   (480)

/* LCD settings */
#define EXAMPLE_LCD_LVGL_FULL_REFRESH           (0)
#define EXAMPLE_LCD_LVGL_DIRECT_MODE            (1)
#define EXAMPLE_LCD_LVGL_AVOID_TEAR             (1)
#define EXAMPLE_LCD_RGB_BOUNCE_BUFFER_MODE      (1)
#define EXAMPLE_LCD_DRAW_BUFF_DOUBLE            (0)
#define EXAMPLE_LCD_DRAW_BUFF_HEIGHT            (100)
#define EXAMPLE_LCD_RGB_BUFFER_NUMS             (2)
#define EXAMPLE_LCD_RGB_BOUNCE_BUFFER_HEIGHT    (10)

/* LCD pins */
#define EXAMPLE_LCD_GPIO_VSYNC     (GPIO_NUM_3)
#define EXAMPLE_LCD_GPIO_HSYNC     (GPIO_NUM_46)
#define EXAMPLE_LCD_GPIO_DE        (GPIO_NUM_17)
#define EXAMPLE_LCD_GPIO_PCLK      (GPIO_NUM_9)
#define EXAMPLE_LCD_GPIO_DISP      (GPIO_NUM_NC)
#define EXAMPLE_LCD_GPIO_DATA0     (GPIO_NUM_10)
#define EXAMPLE_LCD_GPIO_DATA1     (GPIO_NUM_11)
#define EXAMPLE_LCD_GPIO_DATA2     (GPIO_NUM_12)
#define EXAMPLE_LCD_GPIO_DATA3     (GPIO_NUM_13)
#define EXAMPLE_LCD_GPIO_DATA4     (GPIO_NUM_14)
#define EXAMPLE_LCD_GPIO_DATA5     (GPIO_NUM_21)
#define EXAMPLE_LCD_GPIO_DATA6     (GPIO_NUM_47)
#define EXAMPLE_LCD_GPIO_DATA7     (GPIO_NUM_48)
#define EXAMPLE_LCD_GPIO_DATA8     (GPIO_NUM_45)
#define EXAMPLE_LCD_GPIO_DATA9     (GPIO_NUM_38)
#define EXAMPLE_LCD_GPIO_DATA10    (GPIO_NUM_39)
#define EXAMPLE_LCD_GPIO_DATA11    (GPIO_NUM_40)
#define EXAMPLE_LCD_GPIO_DATA12    (GPIO_NUM_41)
#define EXAMPLE_LCD_GPIO_DATA13    (GPIO_NUM_42)
#define EXAMPLE_LCD_GPIO_DATA14    (GPIO_NUM_2)
#define EXAMPLE_LCD_GPIO_DATA15    (GPIO_NUM_1)

/* Touch settings */
#define EXAMPLE_TOUCH_I2C_NUM       (0)
#define EXAMPLE_TOUCH_I2C_CLK_HZ    (400000)

/* LCD touch pins */
#define EXAMPLE_TOUCH_I2C_SCL       (GPIO_NUM_18)
#define EXAMPLE_TOUCH_I2C_SDA       (GPIO_NUM_8)

#define EXAMPLE_LCD_PANEL_35HZ_RGB_TIMING()  \
    {                                               \
        .pclk_hz = 18 * 1000 * 1000,                \
        .h_res = EXAMPLE_LCD_H_RES,                 \
        .v_res = EXAMPLE_LCD_V_RES,                 \
        .hsync_pulse_width = 40,                    \
        .hsync_back_porch = 40,                     \
        .hsync_front_porch = 48,                    \
        .vsync_pulse_width = 23,                    \
        .vsync_back_porch = 32,                     \
        .vsync_front_porch = 13,                    \
        .flags.pclk_active_neg = true,              \
    }

static const char *TAG = "EXAMPLE";

// LVGL image declare
LV_IMG_DECLARE(esp_logo)

/* LCD IO and panel */
static esp_lcd_panel_handle_t lcd_panel = NULL;
static esp_lcd_touch_handle_t touch_handle = NULL;

/* LVGL display and touch */
static lv_display_t *lvgl_disp = NULL;
static lv_indev_t *lvgl_touch_indev = NULL;

static esp_err_t app_lcd_init(void)
{
    esp_err_t ret = ESP_OK;

    /* LCD initialization */
    ESP_LOGI(TAG, "Initialize RGB panel");
    esp_lcd_rgb_panel_config_t panel_conf = {
        .clk_src = LCD_CLK_SRC_PLL160M,
#if ESP_IDF_VERSION < ESP_IDF_VERSION_VAL(5, 3, 0)
        .psram_trans_align = 64,
#else
        .dma_burst_size = 64,
#endif
        .data_width = 16,
#if ESP_IDF_VERSION >= ESP_IDF_VERSION_VAL(6,0,0)
        .in_color_format = LCD_COLOR_FMT_RGB565,
#else
        .bits_per_pixel = 16,
#endif
        .de_gpio_num = EXAMPLE_LCD_GPIO_DE,
        .pclk_gpio_num = EXAMPLE_LCD_GPIO_PCLK,
        .vsync_gpio_num = EXAMPLE_LCD_GPIO_VSYNC,
        .hsync_gpio_num = EXAMPLE_LCD_GPIO_HSYNC,
        .disp_gpio_num = EXAMPLE_LCD_GPIO_DISP,
        .data_gpio_nums = {
            EXAMPLE_LCD_GPIO_DATA0,
            EXAMPLE_LCD_GPIO_DATA1,
            EXAMPLE_LCD_GPIO_DATA2,
            EXAMPLE_LCD_GPIO_DATA3,
            EXAMPLE_LCD_GPIO_DATA4,
            EXAMPLE_LCD_GPIO_DATA5,
            EXAMPLE_LCD_GPIO_DATA6,
            EXAMPLE_LCD_GPIO_DATA7,
            EXAMPLE_LCD_GPIO_DATA8,
            EXAMPLE_LCD_GPIO_DATA9,
            EXAMPLE_LCD_GPIO_DATA10,
            EXAMPLE_LCD_GPIO_DATA11,
            EXAMPLE_LCD_GPIO_DATA12,
            EXAMPLE_LCD_GPIO_DATA13,
            EXAMPLE_LCD_GPIO_DATA14,
            EXAMPLE_LCD_GPIO_DATA15,
        },
        .timings = EXAMPLE_LCD_PANEL_35HZ_RGB_TIMING(),
        .flags.fb_in_psram = 1,
        .num_fbs = EXAMPLE_LCD_RGB_BUFFER_NUMS,
#if EXAMPLE_LCD_RGB_BOUNCE_BUFFER_MODE
        .bounce_buffer_size_px = EXAMPLE_LCD_H_RES * EXAMPLE_LCD_RGB_BOUNCE_BUFFER_HEIGHT,
#endif
    };
    ESP_GOTO_ON_ERROR(esp_lcd_new_rgb_panel(&panel_conf, &lcd_panel), err, TAG, "RGB init failed");
    ESP_GOTO_ON_ERROR(esp_lcd_panel_init(lcd_panel), err, TAG, "LCD init failed");

    return ret;

err:
    if (lcd_panel) {
        esp_lcd_panel_del(lcd_panel);
    }
    return ret;
}

static esp_err_t app_touch_init(void)
{
    /* Initilize I2C */
    i2c_master_bus_handle_t i2c_handle = NULL;
    const i2c_master_bus_config_t i2c_config = {
        .i2c_port = EXAMPLE_TOUCH_I2C_NUM,
        .sda_io_num = EXAMPLE_TOUCH_I2C_SDA,
        .scl_io_num = EXAMPLE_TOUCH_I2C_SCL,
        .clk_source = I2C_CLK_SRC_DEFAULT,
    };
    ESP_RETURN_ON_ERROR(i2c_new_master_bus(&i2c_config, &i2c_handle), TAG, "");

    /* Initialize touch HW */
    const esp_lcd_touch_config_t tp_cfg = {
        .x_max = EXAMPLE_LCD_H_RES,
        .y_max = EXAMPLE_LCD_V_RES,
        .rst_gpio_num = GPIO_NUM_NC,
        .int_gpio_num = GPIO_NUM_NC,
        .levels = {
            .reset = 0,
            .interrupt = 0,
        },
        .flags = {
            .swap_xy = 0,
            .mirror_x = 0,
            .mirror_y = 0,
        },
    };
    esp_lcd_panel_io_handle_t tp_io_handle = NULL;
    esp_lcd_panel_io_i2c_config_t tp_io_config = ESP_LCD_TOUCH_IO_I2C_GT1151_CONFIG();
    tp_io_config.scl_speed_hz = EXAMPLE_TOUCH_I2C_CLK_HZ;
    ESP_RETURN_ON_ERROR(esp_lcd_new_panel_io_i2c(i2c_handle, &tp_io_config, &tp_io_handle), TAG, "");
    return esp_lcd_touch_new_i2c_gt1151(tp_io_handle, &tp_cfg, &touch_handle);
}

static esp_err_t app_lvgl_init(void)
{
    /* Initialize LVGL */
    const lvgl_port_cfg_t lvgl_cfg = {
        .task_priority = 4,         /* LVGL task priority */
        .task_stack = 6144,         /* LVGL task stack size */
        .task_affinity = -1,        /* LVGL task pinned to core (-1 is no affinity) */
        .task_max_sleep_ms = 500,   /* Maximum sleep in LVGL task */
        .timer_period_ms = 5        /* LVGL timer tick period in ms */
    };
    ESP_RETURN_ON_ERROR(lvgl_port_init(&lvgl_cfg), TAG, "LVGL port initialization failed");

    uint32_t buff_size = EXAMPLE_LCD_H_RES * EXAMPLE_LCD_DRAW_BUFF_HEIGHT;
#if EXAMPLE_LCD_LVGL_FULL_REFRESH || EXAMPLE_LCD_LVGL_DIRECT_MODE
    buff_size = EXAMPLE_LCD_H_RES * EXAMPLE_LCD_V_RES;
#endif

    /* Add LCD screen */
    ESP_LOGD(TAG, "Add LCD screen");
    const lvgl_port_display_cfg_t disp_cfg = {
        .panel_handle = lcd_panel,
        .buffer_size = buff_size,
        .double_buffer = EXAMPLE_LCD_DRAW_BUFF_DOUBLE,
        .hres = EXAMPLE_LCD_H_RES,
        .vres = EXAMPLE_LCD_V_RES,
        .monochrome = false,
#if LVGL_VERSION_MAJOR >= 9
        .color_format = LV_COLOR_FORMAT_RGB565,
#endif
        .rotation = {
            .swap_xy = false,
            .mirror_x = false,
            .mirror_y = false,
        },
        .flags = {
            .buff_dma = false,
            .buff_spiram = false,
#if EXAMPLE_LCD_LVGL_FULL_REFRESH
            .full_refresh = true,
#elif EXAMPLE_LCD_LVGL_DIRECT_MODE
            .direct_mode = true,
#endif
#if LVGL_VERSION_MAJOR >= 9
            .swap_bytes = false,
#endif
        }
    };
    const lvgl_port_display_rgb_cfg_t rgb_cfg = {
        .flags = {
#if EXAMPLE_LCD_RGB_BOUNCE_BUFFER_MODE
            .bb_mode = true,
#else
            .bb_mode = false,
#endif
#if EXAMPLE_LCD_LVGL_AVOID_TEAR
            .avoid_tearing = true,
#else
            .avoid_tearing = false,
#endif
        }
    };
    lvgl_disp = lvgl_port_add_disp_rgb(&disp_cfg, &rgb_cfg);

    /* Add touch input (for selected screen) */
    const lvgl_port_touch_cfg_t touch_cfg = {
        .disp = lvgl_disp,
        .handle = touch_handle,
    };
    lvgl_touch_indev = lvgl_port_add_touch(&touch_cfg);

    return ESP_OK;
}

void app_main(void)
{
    /* LCD HW initialization */
    ESP_ERROR_CHECK(app_lcd_init());

    /* Touch initialization */
    ESP_ERROR_CHECK(app_touch_init());

    /* LVGL initialization */
    ESP_ERROR_CHECK(app_lvgl_init());

    /* Show LVGL objects */
    lvgl_port_lock(0);
    lv_demo_music();
    lvgl_port_unlock();

}
