OLIMEX/ESP32-P4-PC/SOFTWARE/ESP-IDF/p4_production_test/components/esp-bsp/examples/display_rotation/main/main.c

/*
 * SPDX-FileCopyrightText: 2022-2024 Espressif Systems (Shanghai) CO LTD
 *
 * SPDX-License-Identifier: CC0-1.0
 */

/**
 * @file
 * @brief BSP Display Rotation Example
 * @details Rotate screen using buttons or an accelerometer (`BSP_CAPS_IMU`, if available)
 * @example https://espressif.github.io/esp-launchpad/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
 */

#include "esp_log.h"
#include "bsp/esp-bsp.h"
#include "lvgl.h"
#if BSP_CAPS_IMU
#include "icm42670.h"
#endif

static const char *TAG = "example";

// LVGL image declare
LV_IMG_DECLARE(esp_logo)

static lv_disp_t *display;
static lv_obj_t *lbl_rotation;
static lv_disp_rotation_t rotation = LV_DISPLAY_ROTATION_0;
#if BSP_CAPS_IMU
static icm42670_handle_t imu = NULL;
#endif


/*******************************************************************************
* Private functions
*******************************************************************************/

static uint16_t app_lvgl_get_rotation_degrees(lv_disp_rotation_t rotation)
{
    switch (rotation) {
    case LV_DISPLAY_ROTATION_0:
        return 0;
    case LV_DISPLAY_ROTATION_90:
        return 90;
    case LV_DISPLAY_ROTATION_180:
        return 180;
    case LV_DISPLAY_ROTATION_270:
        return 270;
    }

    return 0;
}

static void app_lvgl_btn_right_cb(lv_event_t *e)
{
    if (rotation == LV_DISPLAY_ROTATION_270) {
        rotation = LV_DISPLAY_ROTATION_0;
    } else {
        rotation++;
    }

    /* Rotate display */
    bsp_display_lock(0);
    bsp_display_rotate(display, rotation);
    lv_label_set_text_fmt(lbl_rotation, "Rotation %d°", app_lvgl_get_rotation_degrees(rotation));
    bsp_display_unlock();

}

static void app_lvgl_btn_left_cb(lv_event_t *e)
{
    if (rotation == LV_DISPLAY_ROTATION_0) {
        rotation = LV_DISPLAY_ROTATION_270;
    } else {
        rotation--;
    }

    /* Rotate display */
    bsp_display_lock(0);
    bsp_display_rotate(display, rotation);
    lv_label_set_text_fmt(lbl_rotation, "Rotation %d°", app_lvgl_get_rotation_degrees(rotation));
    bsp_display_unlock();
}

static void app_lvgl_display(void)
{
    lv_obj_t *scr = lv_scr_act();
    lv_obj_t *lbl;
    bsp_display_lock(0);

    // Create image
    lv_obj_t *img_logo = lv_img_create(scr);
    lv_img_set_src(img_logo, &esp_logo);
    lv_obj_align(img_logo, LV_ALIGN_TOP_MID, 0, 20);

    lbl_rotation = lv_label_create(scr);
    lv_label_set_text(lbl_rotation, "Rotation 0°");
    lv_obj_align(lbl_rotation, LV_ALIGN_CENTER, 0, 20);

#if BSP_CAPS_IMU
    if (!imu)
#endif
    {
        lv_obj_t *cont_row = lv_obj_create(scr);
        lv_obj_set_size(cont_row, BSP_LCD_V_RES - 10, 50);
        lv_obj_align(cont_row, LV_ALIGN_BOTTOM_MID, 0, -20);
        lv_obj_set_flex_flow(cont_row, LV_FLEX_FLOW_ROW);
        lv_obj_set_style_pad_top(cont_row, 5, 0);
        lv_obj_set_style_pad_bottom(cont_row, 5, 0);
        lv_obj_set_style_pad_left(cont_row, 5, 0);
        lv_obj_set_style_pad_right(cont_row, 5, 0);
        lv_obj_set_flex_align(cont_row, LV_FLEX_ALIGN_CENTER, LV_FLEX_ALIGN_CENTER, LV_FLEX_ALIGN_CENTER);

        /* Button rotate left */
        lv_obj_t *btn_left = lv_btn_create(cont_row);
        lbl = lv_label_create(btn_left);
        lv_label_set_text_static(lbl, LV_SYMBOL_LEFT" Left");
        lv_obj_align(btn_left, LV_ALIGN_BOTTOM_LEFT, 30, -30);
        /* Button event */
        lv_obj_add_event_cb(btn_left, app_lvgl_btn_left_cb, LV_EVENT_CLICKED, scr);

        lbl = lv_label_create(cont_row);
        lv_label_set_text_static(lbl, " rotate ");

        /* Button rotate right */
        lv_obj_t *btn_right = lv_btn_create(cont_row);
        lbl = lv_label_create(btn_right);
        lv_label_set_text_static(lbl, "Right "LV_SYMBOL_RIGHT);
        lv_obj_align(btn_right, LV_ALIGN_BOTTOM_LEFT, 30, -30);
        /* Button event */
        lv_obj_add_event_cb(btn_right, app_lvgl_btn_right_cb, LV_EVENT_CLICKED, scr);

        /* Input device group */
        lv_indev_t *indev = bsp_display_get_input_dev();
        if (indev && lv_indev_get_type(indev) == LV_INDEV_TYPE_ENCODER) {
            lv_group_t *main_group = lv_group_create();
            lv_group_add_obj(main_group, btn_left);
            lv_group_add_obj(main_group, btn_right);
            lv_indev_set_group(indev, main_group);
            ESP_LOGI(TAG, "Input device group was set.");
        }
    }

    bsp_display_unlock();
}

#if BSP_CAPS_IMU
static void app_imu_init(void)
{
    i2c_master_bus_handle_t i2c_handle = bsp_i2c_get_handle();
    ESP_ERROR_CHECK(icm42670_create(i2c_handle, ICM42670_I2C_ADDRESS, &imu));
    if (imu) {
        /* Configuration of the accelerometer and gyroscope */
        const icm42670_cfg_t imu_cfg = {
            .acce_fs = ACCE_FS_2G,
            .acce_odr = ACCE_ODR_400HZ,
            .gyro_fs = GYRO_FS_2000DPS,
            .gyro_odr = GYRO_ODR_400HZ,
        };
        ESP_ERROR_CHECK(icm42670_config(imu, &imu_cfg));

        /* Set accelerometer and gyroscope to ON */
        icm42670_acce_set_pwr(imu, ACCE_PWR_LOWNOISE);
        icm42670_gyro_set_pwr(imu, GYRO_PWR_LOWNOISE);
    }
}

static void app_imu_read(void)
{
    icm42670_value_t acce_val;
    icm42670_get_acce_value(imu, &acce_val);
    ESP_LOGI(TAG, "ACCE val: %.2f, %.2f, %.2f", acce_val.x, acce_val.y, acce_val.z);

    icm42670_value_t gyro_val;
    icm42670_get_gyro_value(imu, &gyro_val);
    ESP_LOGI(TAG, "GYRO val: %.2f, %.2f, %.2f", gyro_val.x, gyro_val.y, gyro_val.z);

    float val;
    icm42670_get_temp_value(imu, &val);
    ESP_LOGI(TAG, "TEMP val: %.2f", val);

    complimentary_angle_t angle;
    icm42670_complimentory_filter(imu, &acce_val, &gyro_val, &angle);
    ESP_LOGI(TAG, "Angle roll: %.2f pitch: %.2f ", angle.roll, angle.pitch);

    if (acce_val.y < -0.6) {
        if (rotation != LV_DISPLAY_ROTATION_0) {
            rotation = LV_DISPLAY_ROTATION_0;
            bsp_display_lock(0);
            bsp_display_rotate(display, rotation);
            lv_label_set_text_fmt(lbl_rotation, "Rotation %d°", app_lvgl_get_rotation_degrees(rotation));
            bsp_display_unlock();
        }
    } else if (acce_val.y > 0.6) {
        if (rotation != LV_DISPLAY_ROTATION_180) {
            rotation = LV_DISPLAY_ROTATION_180;
            bsp_display_lock(0);
            bsp_display_rotate(display, rotation);
            lv_label_set_text_fmt(lbl_rotation, "Rotation %d°", app_lvgl_get_rotation_degrees(rotation));
            bsp_display_unlock();
        }
    } else if (acce_val.x > 0.6) {
        if (rotation != LV_DISPLAY_ROTATION_270) {
            rotation = LV_DISPLAY_ROTATION_270;
            bsp_display_lock(0);
            bsp_display_rotate(display, rotation);
            lv_label_set_text_fmt(lbl_rotation, "Rotation %d°", app_lvgl_get_rotation_degrees(rotation));
            bsp_display_unlock();
        }
    } else if (acce_val.x < -0.6) {
        if (rotation != LV_DISPLAY_ROTATION_90) {
            rotation = LV_DISPLAY_ROTATION_90;
            bsp_display_lock(0);
            bsp_display_rotate(display, rotation);
            lv_label_set_text_fmt(lbl_rotation, "Rotation %d°", app_lvgl_get_rotation_degrees(rotation));
            bsp_display_unlock();
        }
    }

}
#endif

void app_main(void)
{
    /* Initialize display and LVGL */
    display = bsp_display_start();

    /* Set display brightness to 100% */
    bsp_display_backlight_on();

#if BSP_CAPS_IMU
    app_imu_init();
#endif

    /* Add and show objects on display */
    app_lvgl_display();

    ESP_LOGI(TAG, "Example initialization done.");

#if BSP_CAPS_IMU
    while (1) {
        app_imu_read();
        vTaskDelay(pdMS_TO_TICKS(500));
    }
#endif
}
