OLIMEX/ESP32-P4-PC/SOFTWARE/ESP-IDF/p4_production_test/components/esp-bsp/examples/display/main/main.c

/*
 * SPDX-FileCopyrightText: 2021-2025 Espressif Systems (Shanghai) CO LTD
 *
 * SPDX-License-Identifier: CC0-1.0
 */

/**
 * @file
 * @brief BSP Display Example
 * @details Show an image on the screen with a simple startup animation (LVGL)
 * @example https://espressif.github.io/esp-launchpad/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
 */

#include <stdio.h>
#include "bsp/esp-bsp.h"
#include "lvgl.h"
#include "esp_log.h"

extern void example_lvgl_demo_ui(lv_obj_t *scr);

void app_main(void)
{
    bsp_display_start();

    ESP_LOGI("example", "Display LVGL animation");
    bsp_display_lock(0);
    lv_obj_t *scr = lv_disp_get_scr_act(NULL);
#if (CONFIG_ESP_LCD_TOUCH_MAX_POINTS > 1 && CONFIG_LV_USE_GESTURE_RECOGNITION)
    lv_indev_t *indev = bsp_display_get_input_dev();
    lv_indev_set_rotation_rad_threshold(indev, 0.15f);
#endif
    example_lvgl_demo_ui(scr);

    bsp_display_unlock();
    bsp_display_backlight_on();
}
