OLIMEX/ESP32-P4-PC/SOFTWARE/ESP-IDF/p4_production_test/components/esp-bsp/examples/display_lvgl_demos/main/main.c

/*
 * SPDX-FileCopyrightText: 2021-2024 Espressif Systems (Shanghai) CO LTD
 *
 * SPDX-License-Identifier: CC0-1.0
 */

/**
 * @file
 * @brief BSP LVGL Demos Example
 * @details Run the LVGL demo player - all LVGL examples are included (LVGL)
 * @example https://espressif.github.io/esp-launchpad/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
 */

#include "freertos/FreeRTOS.h"
#include "freertos/task.h"
#include "esp_log.h"

#include "lv_demos.h"
#include "bsp/esp-bsp.h"

static char *TAG = "app_main";

#define LOG_MEM_INFO    (0)

void app_main(void)
{
    /* Initialize display and LVGL */
    bsp_display_start();

#if CONFIG_BSP_DISPLAY_LVGL_AVOID_TEAR
    ESP_LOGI(TAG, "Avoid lcd tearing effect");
#if CONFIG_BSP_DISPLAY_LVGL_FULL_REFRESH
    ESP_LOGI(TAG, "LVGL full-refresh");
#elif CONFIG_BSP_DISPLAY_LVGL_DIRECT_MODE
    ESP_LOGI(TAG, "LVGL direct-mode");
#endif
#endif

    /* Set display brightness to 100% */
    bsp_display_backlight_on();

    ESP_LOGI(TAG, "Display LVGL demo");
    bsp_display_lock(0);
    // lv_demo_widgets();      /* A widgets example */
    lv_demo_music();        /* A modern, smartphone-like music player demo. */
    // lv_demo_stress();       /* A stress test for LVGL. */
    // lv_demo_benchmark();    /* A demo to measure the performance of LVGL or to compare different settings. */
    bsp_display_unlock();

#if LOG_MEM_INFO
    static char buffer[128];    /* Make sure buffer is enough for `sprintf` */
    while (1) {
        sprintf(buffer, "   Biggest /     Free /    Total\n"
                "\t  SRAM : [%8d / %8d / %8d]\n"
                "\t PSRAM : [%8d / %8d / %8d]",
                heap_caps_get_largest_free_block(MALLOC_CAP_INTERNAL),
                heap_caps_get_free_size(MALLOC_CAP_INTERNAL),
                heap_caps_get_total_size(MALLOC_CAP_INTERNAL),
                heap_caps_get_largest_free_block(MALLOC_CAP_SPIRAM),
                heap_caps_get_free_size(MALLOC_CAP_SPIRAM),
                heap_caps_get_total_size(MALLOC_CAP_SPIRAM));
        ESP_LOGI("MEM", "%s", buffer);

        vTaskDelay(pdMS_TO_TICKS(500));
    }
#endif
}
