OLIMEX/ESP32-P4-PC/SOFTWARE/ESP-IDF/p4_production_test/components/esp-bsp/bsp/esp32_c3_lcdkit/esp32_c3_lcdkit.c

/*
 * SPDX-FileCopyrightText: 2023-2025 Espressif Systems (Shanghai) CO LTD
 *
 * SPDX-License-Identifier: Apache-2.0
 */

#include "driver/gpio.h"
#include "driver/ledc.h"
#include "driver/spi_master.h"
#include "esp_err.h"
#include "esp_log.h"
#include "esp_spiffs.h"
#include "esp_lcd_panel_io.h"
#include "esp_lcd_panel_vendor.h"
#include "esp_lcd_panel_ops.h"
#include "driver/rmt_tx.h"
#include "led_strip.h"
#include "led_strip_interface.h"

#include "bsp/esp-bsp.h"
#include "bsp/display.h"
#include "bsp_err_check.h"
#include "esp_lcd_gc9a01.h"
#include "iot_knob.h"
#include "button_gpio.h"
#include "esp_lvgl_port.h"
#include "esp_codec_dev_defaults.h"

static const char *TAG = "ESP32-C3-LCDKit";

/**
 * @brief ESP32-C3-LCDkit I2S pinout
 *
 * Can be used for i2s_pdm_tx_gpio_config_t and/or i2s_pdm_tx_config_t initialization
 */
#define BSP_I2S_GPIO_CFG       \
    {                          \
        .clk = BSP_I2S_CLK,    \
        .dout = BSP_I2S_DOUT,  \
        .invert_flags = {      \
            .clk_inv = false, \
        },                     \
    }

/**
 * @brief Mono Duplex I2S configuration structure
 *
 * This configuration is used by default in bsp_audio_init()
 */
#define BSP_I2S_DUPLEX_MONO_CFG(_sample_rate)                                                         \
    {                                                                                                 \
        .clk_cfg = I2S_PDM_TX_CLK_DEFAULT_CONFIG(_sample_rate),                                          \
        .slot_cfg = I2S_PDM_TX_SLOT_DEFAULT_CONFIG(I2S_DATA_BIT_WIDTH_16BIT, I2S_SLOT_MODE_MONO), \
        .gpio_cfg = BSP_I2S_GPIO_CFG,                                                                 \
    }

static lv_indev_t *disp_indev = NULL;
static led_strip_handle_t led_strip;

static const audio_codec_data_if_t *i2s_data_if = NULL;  /* Codec data interface */
static i2s_chan_handle_t i2s_tx_chan;

/**
 * @brief led configuration structure
 *
 * This configuration is used by default in bsp_led_init()
 */
static const led_strip_config_t bsp_strip_config = {
    .strip_gpio_num = BSP_RGB_CTRL,
    .max_leds = 1,
    .led_model = LED_MODEL_WS2812,
    .flags.invert_out = false,
};

static const led_strip_rmt_config_t bsp_rmt_config = {
    .clk_src = RMT_CLK_SRC_DEFAULT,
    .resolution_hz = 10 * 1000 * 1000,
    .flags.with_dma = false,
};

static const button_gpio_config_t bsp_encoder_btn_config = {
    .gpio_num = BSP_BTN_PRESS,
    .active_level = 0,
};

static const knob_config_t bsp_encoder_a_b_config = {
    .default_direction = 0,
    .gpio_encoder_a = BSP_ENCODER_A,
    .gpio_encoder_b = BSP_ENCODER_B,
};

esp_err_t bsp_led_init()
{
    ESP_LOGI(TAG, "BLINK_GPIO setting %d", bsp_strip_config.strip_gpio_num);

    ESP_ERROR_CHECK(led_strip_new_rmt_device(&bsp_strip_config, &bsp_rmt_config, &led_strip));
    led_strip_set_pixel(led_strip, 0, 0x00, 0x00, 0x00);
    led_strip_refresh(led_strip);

    return ESP_OK;
}

esp_err_t bsp_led_rgb_set(uint8_t r, uint8_t g, uint8_t b)
{
    esp_err_t ret = ESP_OK;
    uint32_t index = 0;

    ret |= led_strip_set_pixel(led_strip, index, r, g, b);
    ret |= led_strip_refresh(led_strip);
    return ret;
}

esp_err_t bsp_audio_init(const i2s_pdm_tx_config_t *i2s_config, i2s_chan_handle_t *tx_channel)
{
    if (i2s_tx_chan && i2s_data_if) {
        if (tx_channel) {
            *tx_channel = i2s_tx_chan;
        }

        /* Audio was initialized before */
        return ESP_OK;
    }

    /* Setup I2S peripheral */
    i2s_chan_config_t chan_cfg = I2S_CHANNEL_DEFAULT_CONFIG(I2S_NUM_0, I2S_ROLE_MASTER);
    chan_cfg.auto_clear = true; // Auto clear the legacy data in the DMA buffer
    BSP_ERROR_CHECK_RETURN_ERR(i2s_new_channel(&chan_cfg, tx_channel, NULL));

    /* Setup I2S channels */
    const i2s_pdm_tx_config_t pdm_cfg_default = BSP_I2S_DUPLEX_MONO_CFG(44100);
    const i2s_pdm_tx_config_t *p_i2s_cfg = &pdm_cfg_default;
    if (i2s_config != NULL) {
        p_i2s_cfg = i2s_config;
    }

    if (tx_channel != NULL) {
        BSP_ERROR_CHECK_RETURN_ERR(i2s_channel_init_pdm_tx_mode(*tx_channel, p_i2s_cfg));
        BSP_ERROR_CHECK_RETURN_ERR(i2s_channel_enable(*tx_channel));
    }

    audio_codec_i2s_cfg_t i2s_cfg = {
        .port = I2S_NUM_0,
        .rx_handle = NULL,
        .tx_handle = i2s_tx_chan,
    };
    i2s_data_if = audio_codec_new_i2s_data(&i2s_cfg);
    BSP_NULL_CHECK(i2s_data_if, NULL);

    return ESP_OK;
}

esp_codec_dev_handle_t bsp_audio_codec_speaker_init(void)
{
    if (i2s_tx_chan == NULL || i2s_data_if == NULL) {
        /* Configure I2S peripheral and Power Amplifier */
        BSP_ERROR_CHECK_RETURN_ERR(bsp_audio_init(NULL, &i2s_tx_chan));
    }
    assert(i2s_data_if);

    esp_codec_dev_cfg_t codec_dev_cfg = {
        .dev_type = ESP_CODEC_DEV_TYPE_OUT,
        .codec_if = NULL,
        .data_if = i2s_data_if,
    };
    return esp_codec_dev_new(&codec_dev_cfg);
}

esp_err_t bsp_spiffs_mount(void)
{
    esp_vfs_spiffs_conf_t conf = {
        .base_path = CONFIG_BSP_SPIFFS_MOUNT_POINT,
        .partition_label = CONFIG_BSP_SPIFFS_PARTITION_LABEL,
        .max_files = CONFIG_BSP_SPIFFS_MAX_FILES,
#ifdef CONFIG_BSP_SPIFFS_FORMAT_ON_MOUNT_FAIL
        .format_if_mount_failed = true,
#else
        .format_if_mount_failed = false,
#endif
    };

    esp_err_t ret_val = esp_vfs_spiffs_register(&conf);

    BSP_ERROR_CHECK_RETURN_ERR(ret_val);

    size_t total = 0, used = 0;
    ret_val = esp_spiffs_info(conf.partition_label, &total, &used);
    if (ret_val != ESP_OK) {
        ESP_LOGE(TAG, "Failed to get SPIFFS partition information (%s)", esp_err_to_name(ret_val));
    } else {
        ESP_LOGI(TAG, "Partition size: total: %d, used: %d", total, used);
    }

    return ret_val;
}

esp_err_t bsp_spiffs_unmount(void)
{
    return esp_vfs_spiffs_unregister(CONFIG_BSP_SPIFFS_PARTITION_LABEL);
}

static lv_display_t *bsp_display_lcd_init(const bsp_display_cfg_t *cfg)
{
    assert(cfg != NULL);
    esp_lcd_panel_io_handle_t io_handle = NULL;
    esp_lcd_panel_handle_t panel_handle = NULL;
    const bsp_display_config_t bsp_disp_cfg = {
        .max_transfer_sz = BSP_LCD_H_RES * 80 * sizeof(uint16_t),
    };
    BSP_ERROR_CHECK_RETURN_NULL(bsp_display_new(&bsp_disp_cfg, &panel_handle, &io_handle));

    esp_lcd_panel_disp_on_off(panel_handle, true);

    /* Add LCD screen */
    ESP_LOGD(TAG, "Add LCD screen");
    const lvgl_port_display_cfg_t disp_cfg = {
        .io_handle = io_handle,
        .panel_handle = panel_handle,
        .buffer_size = cfg->buffer_size,
        .double_buffer = cfg->double_buffer,
        .hres = BSP_LCD_H_RES,
        .vres = BSP_LCD_V_RES,
        .monochrome = false,
        /* Rotation values must be same as used in esp_lcd for initial settings of the screen */
        .rotation = {
            .swap_xy = false,
            .mirror_x = true,
            .mirror_y = false,
        },
        .flags = {
            .buff_dma = cfg->flags.buff_dma,
            .buff_spiram = cfg->flags.buff_spiram,
#if LVGL_VERSION_MAJOR >= 9
            .swap_bytes = (BSP_LCD_BIGENDIAN ? true : false),
#endif
        }
    };

    return lvgl_port_add_disp(&disp_cfg);
}

static lv_indev_t *bsp_display_indev_init(lv_display_t *disp)
{

    const button_config_t btn_cfg = {0};
    button_handle_t encoder_btn = NULL;
    BSP_ERROR_CHECK_RETURN_NULL(iot_button_new_gpio_device(&btn_cfg, &bsp_encoder_btn_config, &encoder_btn));

    const lvgl_port_encoder_cfg_t encoder = {
        .disp = disp,
        .encoder_a_b = &bsp_encoder_a_b_config,
        .encoder_enter = encoder_btn
    };

    return lvgl_port_add_encoder(&encoder);
}

// Bit number used to represent command and parameter
#define LCD_CMD_BITS           8
#define LCD_PARAM_BITS         8
#define LCD_LEDC_DUTY_RES      (LEDC_TIMER_10_BIT)
#define LCD_LEDC_CH            CONFIG_BSP_DISPLAY_BRIGHTNESS_LEDC_CH

esp_err_t bsp_display_brightness_init(void)
{
    // Setup LEDC peripheral for PWM backlight control
    const ledc_channel_config_t LCD_backlight_channel = {
        .gpio_num = BSP_LCD_BACKLIGHT,
        .speed_mode = LEDC_LOW_SPEED_MODE,
        .channel = LCD_LEDC_CH,
        .intr_type = LEDC_INTR_DISABLE,
        .timer_sel = LEDC_TIMER_1,
        .duty = 0,
        .hpoint = 0
    };
    const ledc_timer_config_t LCD_backlight_timer = {
        .speed_mode = LEDC_LOW_SPEED_MODE,
        .duty_resolution = LCD_LEDC_DUTY_RES,
        .timer_num = LEDC_TIMER_1,
        .freq_hz = 5000,
        .clk_cfg = LEDC_AUTO_CLK
    };

    BSP_ERROR_CHECK_RETURN_ERR(ledc_timer_config(&LCD_backlight_timer));
    BSP_ERROR_CHECK_RETURN_ERR(ledc_channel_config(&LCD_backlight_channel));

    return ESP_OK;
}

esp_err_t bsp_display_brightness_set(int brightness_percent)
{
    if (brightness_percent > 100) {
        brightness_percent = 100;
    }
    if (brightness_percent < 0) {
        brightness_percent = 0;
    }

    ESP_LOGD(TAG, "Setting LCD backlight: %d%%", brightness_percent);
    uint32_t duty_cycle = (BIT(LCD_LEDC_DUTY_RES) * (brightness_percent)) / 100;
    BSP_ERROR_CHECK_RETURN_ERR(ledc_set_duty(LEDC_LOW_SPEED_MODE, LCD_LEDC_CH, duty_cycle));
    BSP_ERROR_CHECK_RETURN_ERR(ledc_update_duty(LEDC_LOW_SPEED_MODE, LCD_LEDC_CH));

    return ESP_OK;
}

esp_err_t bsp_display_backlight_off(void)
{
    return bsp_display_brightness_set(0);
}

esp_err_t bsp_display_backlight_on(void)
{
    return bsp_display_brightness_set(100);
}

esp_err_t bsp_display_new(const bsp_display_config_t *config, esp_lcd_panel_handle_t *ret_panel, esp_lcd_panel_io_handle_t *ret_io)
{
    esp_err_t ret = ESP_OK;
    assert(config != NULL && config->max_transfer_sz > 0);

    ESP_RETURN_ON_ERROR(bsp_display_brightness_init(), TAG, "Brightness init failed");

    ESP_LOGD(TAG, "Initialize SPI bus");
    const spi_bus_config_t buscfg = {
        .sclk_io_num = BSP_LCD_PCLK,
        .mosi_io_num = BSP_LCD_DATA0,
        .miso_io_num = GPIO_NUM_NC,
        .quadwp_io_num = GPIO_NUM_NC,
        .quadhd_io_num = GPIO_NUM_NC,
        .max_transfer_sz = config->max_transfer_sz,
    };
    ESP_RETURN_ON_ERROR(spi_bus_initialize(BSP_LCD_SPI_NUM, &buscfg, SPI_DMA_CH_AUTO), TAG, "SPI init failed");

    ESP_LOGD(TAG, "Install panel IO");
    const esp_lcd_panel_io_spi_config_t io_config = {
        .dc_gpio_num = BSP_LCD_DC,
        .cs_gpio_num = BSP_LCD_CS,
        .pclk_hz = BSP_LCD_PIXEL_CLOCK_HZ,
        .lcd_cmd_bits = LCD_CMD_BITS,
        .lcd_param_bits = LCD_PARAM_BITS,
        .spi_mode = 0,
        .trans_queue_depth = 10,
    };
    ESP_GOTO_ON_ERROR(esp_lcd_new_panel_io_spi((esp_lcd_spi_bus_handle_t)BSP_LCD_SPI_NUM, &io_config, ret_io), err, TAG, "New panel IO failed");

    ESP_LOGD(TAG, "Install LCD driver");
    const esp_lcd_panel_dev_config_t panel_config = {
        .reset_gpio_num = BSP_LCD_RST, // Shared with Touch reset
        .rgb_ele_order = BSP_LCD_COLOR_SPACE,
        .bits_per_pixel = BSP_LCD_BITS_PER_PIXEL,
    };
    ESP_GOTO_ON_ERROR(esp_lcd_new_panel_gc9a01(*ret_io, &panel_config, ret_panel), err, TAG, "New panel failed");

    BSP_ERROR_CHECK_RETURN_ERR(esp_lcd_panel_reset(*ret_panel));
    BSP_ERROR_CHECK_RETURN_ERR(esp_lcd_panel_init(*ret_panel));
    BSP_ERROR_CHECK_RETURN_ERR(esp_lcd_panel_invert_color(*ret_panel, true));
    BSP_ERROR_CHECK_RETURN_ERR(esp_lcd_panel_mirror(*ret_panel, true, false));
#if ESP_IDF_VERSION >= ESP_IDF_VERSION_VAL(5, 0, 0)
    BSP_ERROR_CHECK_RETURN_ERR(esp_lcd_panel_disp_on_off(*ret_panel, true));
#else
    BSP_ERROR_CHECK_RETURN_ERR(esp_lcd_panel_disp_off(*ret_panel, false));
#endif

    return ret;

err:
    if (*ret_panel) {
        esp_lcd_panel_del(*ret_panel);
    }
    if (*ret_io) {
        esp_lcd_panel_io_del(*ret_io);
    }
    spi_bus_free(BSP_LCD_SPI_NUM);
    return ret;
}

lv_display_t *bsp_display_start(void)
{
    bsp_display_cfg_t cfg = {
        .lvgl_port_cfg = ESP_LVGL_PORT_INIT_CONFIG(),
        .buffer_size = BSP_LCD_H_RES * CONFIG_BSP_LCD_DRAW_BUF_HEIGHT,
#if CONFIG_BSP_LCD_DRAW_BUF_DOUBLE
        .double_buffer = 1,
#else
        .double_buffer = 0,
#endif
        .flags = {
            .buff_dma = true,
            .buff_spiram = false,
        }
    };
    return bsp_display_start_with_config(&cfg);
}

lv_disp_t *bsp_display_start_with_config(const bsp_display_cfg_t *cfg)
{
    lv_disp_t *disp;
    BSP_ERROR_CHECK_RETURN_NULL(lvgl_port_init(&cfg->lvgl_port_cfg));
    BSP_ERROR_CHECK_RETURN_NULL(bsp_display_brightness_init());
    BSP_NULL_CHECK(disp = bsp_display_lcd_init(cfg), NULL);
    BSP_NULL_CHECK(disp_indev = bsp_display_indev_init(disp), NULL);

    return disp;
}

lv_indev_t *bsp_display_get_input_dev(void)
{
    return disp_indev;
}

void bsp_display_rotate(lv_display_t *disp, lv_disp_rotation_t rotation)
{
    lv_disp_set_rotation(disp, rotation);
}

bool bsp_display_lock(uint32_t timeout_ms)
{
    return lvgl_port_lock(timeout_ms);
}

void bsp_display_unlock(void)
{
    lvgl_port_unlock();
}
