OLIMEX/ESP32-P4-PC/SOFTWARE/ESP-IDF/p4_production_test/components/esp-bsp/bsp/esp32_s3_lcd_ev_board/src/esp32_s3_lcd_ev_board.c

/*
 * SPDX-FileCopyrightText: 2022-2025 Espressif Systems (Shanghai) CO LTD
 *
 * SPDX-License-Identifier: Apache-2.0
 */

#include "driver/i2c_master.h"
#include "driver/i2s_std.h"
#include "driver/gpio.h"
#include "esp_codec_dev_defaults.h"
#include "esp_err.h"
#include "esp_io_expander_tca9554.h"
#include "esp_lcd_panel_io.h"
#include "esp_lcd_panel_ops.h"
#include "esp_lcd_panel_rgb.h"
#include "esp_lcd_touch.h"
#include "esp_log.h"
#include "esp_spiffs.h"
#include "iot_button.h"
#include "button_gpio.h"

#include "bsp/esp32_s3_lcd_ev_board.h"
#include "bsp/touch.h"
#include "bsp_err_check.h"
#include "bsp_probe.h"
#include "bsp/config.h"
#include "bsp/display.h"

#if (BSP_CONFIG_NO_GRAPHIC_LIB == 0)
#include "lvgl.h"
#include "esp_lvgl_port.h"
#endif // BSP_CONFIG_NO_GRAPHIC_LIB == 0

#define BSP_ES7210_CODEC_ADDR   (0x82)

/* Can be used for `i2s_std_gpio_config_t` and/or `i2s_std_config_t` initialization */
#define BSP_I2S_GPIO_CFG       \
    {                          \
        .mclk = BSP_I2S_MCLK,  \
        .bclk = BSP_I2S_SCLK,  \
        .ws = BSP_I2S_LCLK,    \
        .dout = BSP_I2S_DOUT,  \
        .din = BSP_I2S_DSIN,   \
        .invert_flags = {      \
            .mclk_inv = false, \
            .bclk_inv = false, \
            .ws_inv = false,   \
        },                     \
    }

/* This configuration is used by default in `bsp_audio_init()` */
#define BSP_I2S_DUPLEX_MONO_CFG(_sample_rate)                                                         \
    {                                                                                                 \
        .clk_cfg = I2S_STD_CLK_DEFAULT_CONFIG(_sample_rate),                                          \
        .slot_cfg = I2S_STD_PHILIP_SLOT_DEFAULT_CONFIG(I2S_DATA_BIT_WIDTH_16BIT, I2S_SLOT_MODE_MONO), \
        .gpio_cfg = BSP_I2S_GPIO_CFG,                                                                 \
    }

static const char *TAG = "S3-LCD-EV-BOARD";

/**
 * @brief I2C handle for BSP usage
 *
 * In IDF v5.4 you can call i2c_master_get_bus_handle(BSP_I2C_NUM, i2c_master_bus_handle_t *ret_handle)
 * from #include "esp_private/i2c_platform.h" to get this handle
 *
 * For IDF 5.2 and 5.3 you must call bsp_i2c_get_handle()
 */
static i2c_master_bus_handle_t i2c_handle = NULL;
static bool i2c_initialized = false;
static const audio_codec_data_if_t *i2s_data_if = NULL;  /* Codec data interface */
static i2s_chan_handle_t i2s_tx_chan = NULL;
static i2s_chan_handle_t i2s_rx_chan = NULL;
static esp_io_expander_handle_t io_expander = NULL; // IO expander tca9554 handle
static adc_oneshot_unit_handle_t bsp_adc_handle = NULL;

#if (BSP_CONFIG_NO_GRAPHIC_LIB == 0)
static lv_display_t *disp;
static lv_indev_t *disp_indev = NULL;
static esp_lcd_touch_handle_t tp;   // LCD touch handle
#endif // (BSP_CONFIG_NO_GRAPHIC_LIB == 0)

static const button_gpio_config_t bsp_button_config[BSP_BUTTON_NUM] = {
    {
        .gpio_num = BSP_BUTTON_BOOT_IO,
        .active_level = 0,
    },
};
/**************************************************************************************************
 *
 * I2C Function
 *
 **************************************************************************************************/
esp_err_t bsp_i2c_init(void)
{
    /* I2C was initialized before */
    if (i2c_initialized) {
        return ESP_OK;
    }

    bsp_module_type_t module_type = bsp_probe_module_type();
    if (module_type == MODULE_TYPE_UNKNOW) {
        ESP_LOGE(TAG, "Unknow module type");
        return ESP_FAIL;
    }
    i2c_master_bus_config_t i2c_config = {
        .i2c_port = BSP_I2C_NUM,
        .sda_io_num = BSP_I2C_SDA,
        .scl_io_num = BSP_I2C_SCL,
        .clk_source = I2C_CLK_SRC_DEFAULT,
    };

    // To compatible with ESP32-S3-WROOM-N16R16V module
    if (module_type == MODULE_TYPE_R16) {
        i2c_config.sda_io_num = BSP_I2C_SDA_R16;
        i2c_config.scl_io_num = BSP_I2C_SCL_R16;
    }

    BSP_ERROR_CHECK_RETURN_ERR(i2c_new_master_bus(&i2c_config, &i2c_handle));

    i2c_initialized = true;
    return ESP_OK;
}

esp_err_t bsp_i2c_deinit(void)
{
    BSP_ERROR_CHECK_RETURN_ERR(i2c_del_master_bus(i2c_handle));
    i2c_initialized = false;
    return ESP_OK;
}

i2c_master_bus_handle_t bsp_i2c_get_handle(void)
{
    bsp_i2c_init();
    return i2c_handle;
}

/**************************************************************************************************
 *
 * SPIFFS Function
 *
 **************************************************************************************************/
esp_err_t bsp_spiffs_mount(void)
{
    esp_vfs_spiffs_conf_t conf = {
        .base_path = CONFIG_BSP_SPIFFS_MOUNT_POINT,
        .partition_label = CONFIG_BSP_SPIFFS_PARTITION_LABEL,
        .max_files = CONFIG_BSP_SPIFFS_MAX_FILES,
#ifdef CONFIG_BSP_SPIFFS_FORMAT_ON_MOUNT_FAIL
        .format_if_mount_failed = true,
#else
        .format_if_mount_failed = false,
#endif
    };

    esp_err_t ret_val = esp_vfs_spiffs_register(&conf);

    BSP_ERROR_CHECK_RETURN_ERR(ret_val);

    size_t total = 0, used = 0;
    ret_val = esp_spiffs_info(conf.partition_label, &total, &used);
    if (ret_val != ESP_OK) {
        ESP_LOGE(TAG, "Failed to get SPIFFS partition information (%s)", esp_err_to_name(ret_val));
    } else {
        ESP_LOGI(TAG, "Partition size: total: %d, used: %d", total, used);
    }

    return ret_val;
}

esp_err_t bsp_spiffs_unmount(void)
{
    return esp_vfs_spiffs_unregister(CONFIG_BSP_SPIFFS_PARTITION_LABEL);
}

/**************************************************************************************************
 *
 * IO Expander Function
 *
 **************************************************************************************************/
esp_io_expander_handle_t bsp_io_expander_init(void)
{
    if (!io_expander) {
        BSP_ERROR_CHECK_RETURN_NULL(esp_io_expander_new_i2c_tca9554(i2c_handle, BSP_IO_EXPANDER_I2C_ADDRESS, &io_expander));
    }

    return io_expander;
}

/**************************************************************************************************
 *
 * I2S Audio Function
 *
 **************************************************************************************************/
esp_err_t bsp_audio_init(const i2s_std_config_t *i2s_config)
{
    esp_err_t ret = ESP_FAIL;
    if (i2s_tx_chan && i2s_rx_chan) {
        /* Audio was initialized before */
        return ESP_OK;
    }

    /* Setup I2S peripheral */
    i2s_chan_config_t chan_cfg = I2S_CHANNEL_DEFAULT_CONFIG(CONFIG_BSP_I2S_NUM, I2S_ROLE_MASTER);
    chan_cfg.auto_clear = true; // Auto clear the legacy data in the DMA buffer
    BSP_ERROR_CHECK_RETURN_ERR(i2s_new_channel(&chan_cfg, &i2s_tx_chan, &i2s_rx_chan));

    /* Setup I2S channels */
    const i2s_std_config_t std_cfg_default = BSP_I2S_DUPLEX_MONO_CFG(22050);
    const i2s_std_config_t *p_i2s_cfg = &std_cfg_default;
    if (i2s_config != NULL) {
        p_i2s_cfg = i2s_config;
    }

    if (i2s_tx_chan != NULL) {
        ESP_GOTO_ON_ERROR(i2s_channel_init_std_mode(i2s_tx_chan, p_i2s_cfg), err, TAG, "I2S channel initialization failed");
        ESP_GOTO_ON_ERROR(i2s_channel_enable(i2s_tx_chan), err, TAG, "I2S enabling failed");
    }
    if (i2s_rx_chan != NULL) {
        ESP_GOTO_ON_ERROR(i2s_channel_init_std_mode(i2s_rx_chan, p_i2s_cfg), err, TAG, "I2S channel initialization failed");
        ESP_GOTO_ON_ERROR(i2s_channel_enable(i2s_rx_chan), err, TAG, "I2S enabling failed");
    }

    audio_codec_i2s_cfg_t i2s_cfg = {
        .port = CONFIG_BSP_I2S_NUM,
        .rx_handle = i2s_rx_chan,
        .tx_handle = i2s_tx_chan,
    };
    i2s_data_if = audio_codec_new_i2s_data(&i2s_cfg);
    BSP_NULL_CHECK_GOTO(i2s_data_if, err);

    /* Setup power amplifier pin, set default to enable */
    bsp_io_expander_init();
    BSP_ERROR_CHECK_RETURN_ERR(esp_io_expander_set_dir(io_expander, BSP_POWER_AMP_IO, IO_EXPANDER_OUTPUT));
    BSP_ERROR_CHECK_RETURN_ERR(esp_io_expander_set_level(io_expander, BSP_POWER_AMP_IO, true));

    return ESP_OK;

err:
    if (i2s_tx_chan) {
        i2s_del_channel(i2s_tx_chan);
    }
    if (i2s_rx_chan) {
        i2s_del_channel(i2s_rx_chan);
    }

    return ret;
}

esp_codec_dev_handle_t bsp_audio_codec_speaker_init(void)
{
    if (i2s_data_if == NULL) {
        /* Initilize I2C */
        BSP_ERROR_CHECK_RETURN_NULL(bsp_i2c_init());
        /* Configure I2S peripheral and Power Amplifier */
        BSP_ERROR_CHECK_RETURN_NULL(bsp_audio_init(NULL));
    }
    assert(i2s_data_if);

    const audio_codec_gpio_if_t *gpio_if = audio_codec_new_gpio();

    audio_codec_i2c_cfg_t i2c_cfg = {
        .port = BSP_I2C_NUM,
        .addr = ES8311_CODEC_DEFAULT_ADDR,
        .bus_handle = i2c_handle,
    };
    const audio_codec_ctrl_if_t *i2c_ctrl_if = audio_codec_new_i2c_ctrl(&i2c_cfg);
    BSP_NULL_CHECK(i2c_ctrl_if, NULL);

    esp_codec_dev_hw_gain_t gain = {
        .pa_voltage = 5.0,
        .codec_dac_voltage = 3.3,
    };

    es8311_codec_cfg_t es8311_cfg = {
        .ctrl_if = i2c_ctrl_if,
        .gpio_if = gpio_if,
        .codec_mode = ESP_CODEC_DEV_WORK_MODE_DAC,
        .pa_pin = GPIO_NUM_NC,  // Don't support IO expander
        .pa_reverted = false,
        .master_mode = false,
        .use_mclk = true,
        .digital_mic = false,
        .invert_mclk = false,
        .invert_sclk = false,
        .hw_gain = gain,
    };
    const audio_codec_if_t *es8311_dev = es8311_codec_new(&es8311_cfg);
    BSP_NULL_CHECK(es8311_dev, NULL);

    esp_codec_dev_cfg_t codec_dev_cfg = {
        .dev_type = ESP_CODEC_DEV_TYPE_OUT,
        .codec_if = es8311_dev,
        .data_if = i2s_data_if,
    };
    return esp_codec_dev_new(&codec_dev_cfg);
}

esp_codec_dev_handle_t bsp_audio_codec_microphone_init(void)
{
    if (i2s_data_if == NULL) {
        /* Initilize I2C */
        BSP_ERROR_CHECK_RETURN_NULL(bsp_i2c_init());
        /* Configure I2S peripheral and Power Amplifier */
        BSP_ERROR_CHECK_RETURN_NULL(bsp_audio_init(NULL));
    }
    assert(i2s_data_if);

    audio_codec_i2c_cfg_t i2c_cfg = {
        .port = BSP_I2C_NUM,
        .addr = BSP_ES7210_CODEC_ADDR,
        .bus_handle = i2c_handle,
    };
    const audio_codec_ctrl_if_t *i2c_ctrl_if = audio_codec_new_i2c_ctrl(&i2c_cfg);
    BSP_NULL_CHECK(i2c_ctrl_if, NULL);

    es7210_codec_cfg_t es7210_cfg = {
        .ctrl_if = i2c_ctrl_if,
    };
    const audio_codec_if_t *es7210_dev = es7210_codec_new(&es7210_cfg);
    BSP_NULL_CHECK(es7210_dev, NULL);

    esp_codec_dev_cfg_t codec_es7210_dev_cfg = {
        .dev_type = ESP_CODEC_DEV_TYPE_IN,
        .codec_if = es7210_dev,
        .data_if = i2s_data_if,
    };
    return esp_codec_dev_new(&codec_es7210_dev_cfg);
}

esp_err_t bsp_audio_poweramp_enable(bool enable)
{
    BSP_ERROR_CHECK_RETURN_ERR(esp_io_expander_set_level(io_expander, BSP_POWER_AMP_IO, (uint8_t)enable));

    return ESP_OK;
}

#if (BSP_CONFIG_NO_GRAPHIC_LIB == 0)
static lv_display_t *bsp_display_lcd_init()
{
    esp_lcd_panel_io_handle_t io_handle = NULL;
    esp_lcd_panel_handle_t panel_handle = NULL;           // LCD panel handle

    bsp_display_config_t disp_config = { 0 };

    BSP_ERROR_CHECK_RETURN_NULL(bsp_display_new(&disp_config, &panel_handle, &io_handle));

    int buffer_size = 0;
#if CONFIG_BSP_DISPLAY_LVGL_AVOID_TEAR
    buffer_size = BSP_LCD_H_RES * BSP_LCD_V_RES;
#else
    buffer_size = BSP_LCD_H_RES * LVGL_BUFFER_HEIGHT;
#endif /* CONFIG_BSP_DISPLAY_LVGL_AVOID_TEAR */

    const lvgl_port_display_cfg_t disp_cfg = {
        .io_handle = io_handle,
        .panel_handle = panel_handle,
        .buffer_size = buffer_size,

        .monochrome = false,
        .hres = BSP_LCD_H_RES,
        .vres = BSP_LCD_V_RES,
#if LVGL_VERSION_MAJOR >= 9
        .color_format = LV_COLOR_FORMAT_RGB565,
#endif

        .rotation = {
            .swap_xy = false,
            .mirror_x = false,
            .mirror_y = false,
        },
        .flags = {
            .buff_dma = false,
#if CONFIG_BSP_DISPLAY_LVGL_PSRAM
            .buff_spiram = false,
#endif
#if CONFIG_BSP_DISPLAY_LVGL_FULL_REFRESH
            .full_refresh = 1,
#elif CONFIG_BSP_DISPLAY_LVGL_DIRECT_MODE
            .direct_mode = 1,
#endif
#if LVGL_VERSION_MAJOR >= 9
            .swap_bytes = false,
#endif
        }
    };
    const lvgl_port_display_rgb_cfg_t rgb_cfg = {
        .flags = {
#if CONFIG_BSP_LCD_RGB_BOUNCE_BUFFER_MODE
            .bb_mode = 1,
#else
            .bb_mode = 0,
#endif
#if CONFIG_BSP_DISPLAY_LVGL_AVOID_TEAR
            .avoid_tearing = true,
#else
            .avoid_tearing = false,
#endif
        }
    };

#if CONFIG_BSP_LCD_RGB_BOUNCE_BUFFER_MODE
    ESP_LOGW(TAG, "CONFIG_BSP_LCD_RGB_BOUNCE_BUFFER_MODE");
#endif

    return lvgl_port_add_disp_rgb(&disp_cfg, &rgb_cfg);
}

static lv_indev_t *bsp_display_indev_init(lv_display_t *disp)
{
    BSP_ERROR_CHECK_RETURN_NULL(bsp_touch_new(NULL, &tp));
    assert(tp);

    /* Add touch input (for selected screen) */
    const lvgl_port_touch_cfg_t touch_cfg = {
        .disp = disp,
        .handle = tp,
    };

    return lvgl_port_add_touch(&touch_cfg);
}

/**********************************************************************************************************
 *
 * Display Function
 *
 **********************************************************************************************************/
lv_display_t *bsp_display_start(void)
{
    bsp_display_cfg_t cfg = {
        .lvgl_port_cfg = ESP_LVGL_PORT_INIT_CONFIG()
    };

    return bsp_display_start_with_config(&cfg);
}

lv_display_t *bsp_display_start_with_config(const bsp_display_cfg_t *cfg)
{
    BSP_ERROR_CHECK_RETURN_NULL(lvgl_port_init(&cfg->lvgl_port_cfg)); /* lvgl task, tick etc*/

    BSP_NULL_CHECK(disp = bsp_display_lcd_init(), NULL);

    BSP_NULL_CHECK(disp_indev = bsp_display_indev_init(disp), NULL);

    return disp;
}

lv_indev_t *bsp_display_get_input_dev(void)
{
    return disp_indev;
}
#endif // (BSP_CONFIG_NO_GRAPHIC_LIB == 0)

esp_err_t bsp_display_brightness_init(void)
{
    ESP_LOGW(TAG, "This board doesn't support to change brightness of LCD");
    return ESP_ERR_NOT_SUPPORTED;
}

esp_err_t bsp_display_brightness_set(int brightness_percent)
{
    ESP_LOGW(TAG, "This board doesn't support to change brightness of LCD");
    return ESP_ERR_NOT_SUPPORTED;
}

esp_err_t bsp_display_backlight_off(void)
{
    return bsp_display_brightness_set(0);
}

esp_err_t bsp_display_backlight_on(void)
{
    return bsp_display_brightness_set(100);
}

#if (BSP_CONFIG_NO_GRAPHIC_LIB == 0)
void bsp_display_rotate(lv_display_t *disp, lv_display_rotation_t rotation)
{
    lv_disp_set_rotation(disp, rotation);
}

bool bsp_display_lock(uint32_t timeout_ms)
{
    return lvgl_port_lock(timeout_ms);
}

void bsp_display_unlock(void)
{
    lvgl_port_unlock();
}
#endif // (BSP_CONFIG_NO_GRAPHIC_LIB == 0)

/**************************************************************************************************
 *
 * Button Function
 *
 **************************************************************************************************/
esp_err_t bsp_button_init(const bsp_button_t btn)
{
    const gpio_config_t button_io_config = {
        .pin_bit_mask = BIT64(btn),
        .mode = GPIO_MODE_INPUT,
        .pull_up_en = GPIO_PULLUP_ENABLE,
        .pull_down_en = GPIO_PULLDOWN_DISABLE,
        .intr_type = GPIO_INTR_DISABLE
    };
    return gpio_config(&button_io_config);
}

bool bsp_button_get(const bsp_button_t btn)
{
    return !(bool)gpio_get_level(btn);
}

esp_err_t bsp_iot_button_create(button_handle_t btn_array[], int *btn_cnt, int btn_array_size)
{
    esp_err_t ret = ESP_OK;
    const button_config_t btn_config = {0};
    if ((btn_array_size < BSP_BUTTON_NUM) ||
            (btn_array == NULL)) {
        return ESP_ERR_INVALID_ARG;
    }

    if (btn_cnt) {
        *btn_cnt = 0;
    }
    for (int i = 0; i < BSP_BUTTON_NUM; i++) {
        ret |= iot_button_new_gpio_device(&btn_config, &bsp_button_config[i], &btn_array[i]);
        if (btn_cnt) {
            (*btn_cnt)++;
        }
    }
    return ret;
}

/**************************************************************************************************
 *
 * ADC Funciton
 *
 **************************************************************************************************/
esp_err_t bsp_adc_initialize(void)
{
    /* ADC was initialized before */
    if (bsp_adc_handle != NULL) {
        return ESP_OK;
    }

    /* Initialize ADC */
    const adc_oneshot_unit_init_cfg_t init_config1 = {
        .unit_id = BSP_ADC_UNIT,
    };
    BSP_ERROR_CHECK_RETURN_ERR(adc_oneshot_new_unit(&init_config1, &bsp_adc_handle));

    return ESP_OK;
}

adc_oneshot_unit_handle_t bsp_adc_get_handle(void)
{
    return bsp_adc_handle;
}
